PubInv/rack-mount-enclosure-for-power/display/OLED_2.4inch_51qNVxTlbsL._SL1050_.jpg

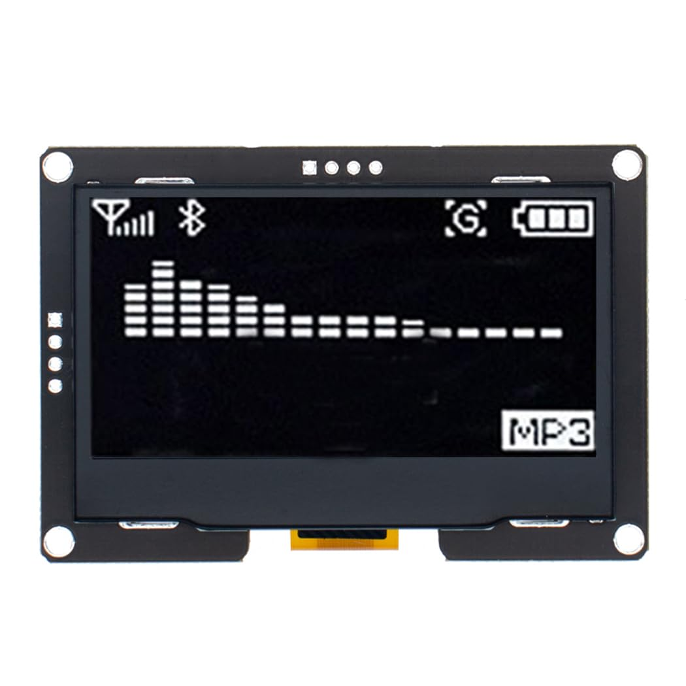
display/OLED_2.4inch_51qNVxTlbsL._SL1050_.jpg
