PubInv/rack-mount-enclosure-for-power/display/RotaryEncoder_51UYRIANXkL._SL1001_.jpg

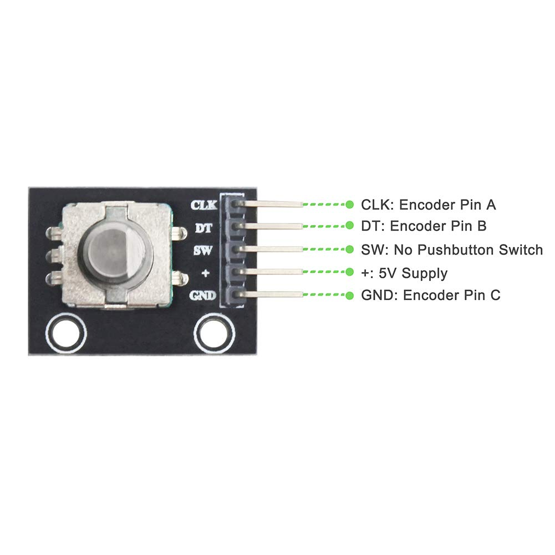
display/RotaryEncoder_51UYRIANXkL._SL1001_.jpg
