PubInv/rack-mount-enclosure-for-power/enclosure/M12BulkHead/MarkedUpDrawing.png

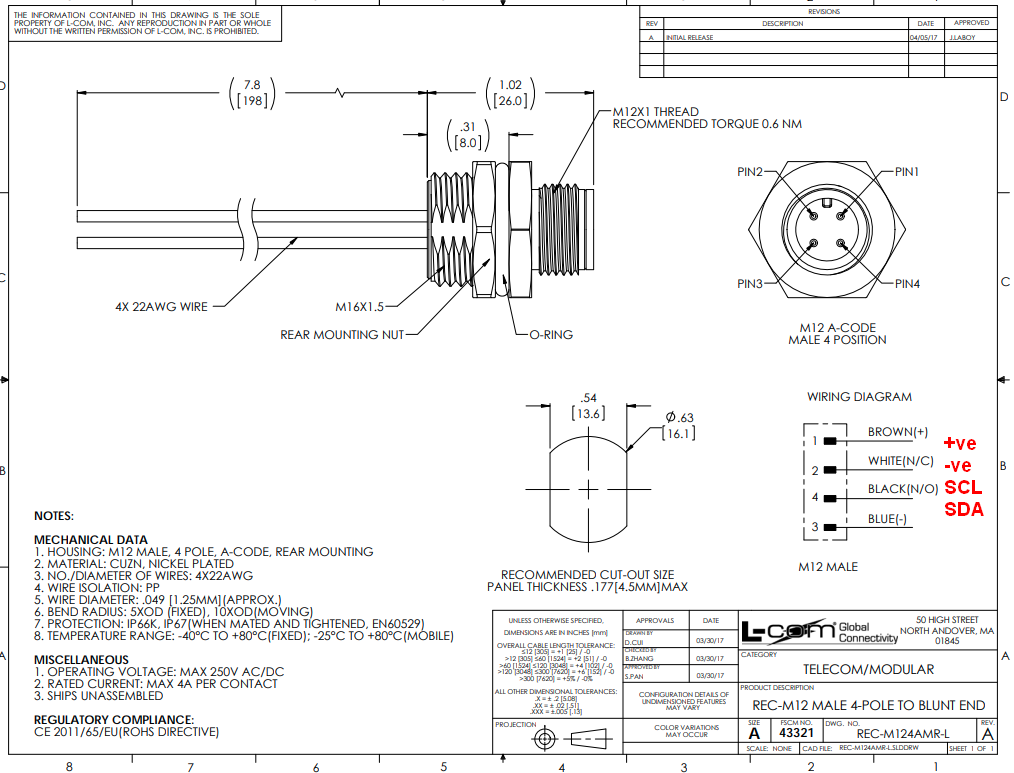
enclosure/M12BulkHead/MarkedUpDrawing.png
