PubInv/rack-mount-enclosure-for-power/enclosure/resources/41Cd8K70ImL.jpg

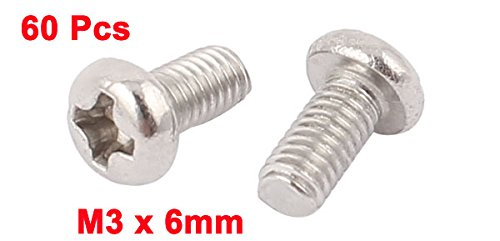
enclosure/resources/41Cd8K70ImL.jpg
