PubInv/rack-mount-enclosure-for-power/enclosure/resources/61TtXo3cijL._AC_SX679_.jpg

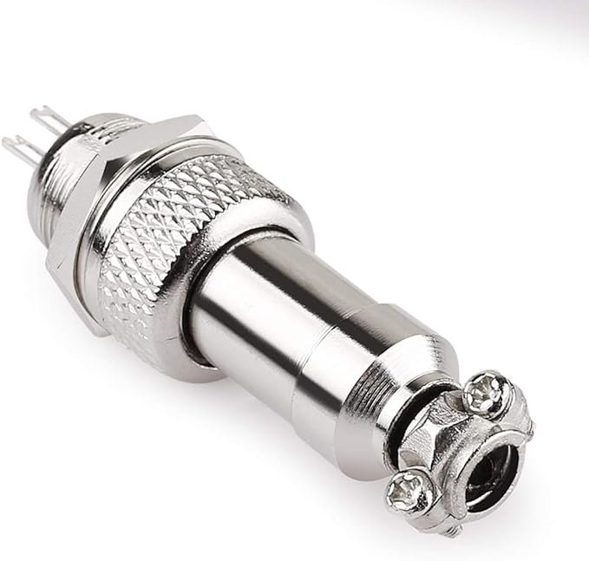
enclosure/resources/61TtXo3cijL._AC_SX679_.jpg
