PubInv/rack-mount-enclosure-for-power/enclosure/resources/PHDR-24VS.jpg

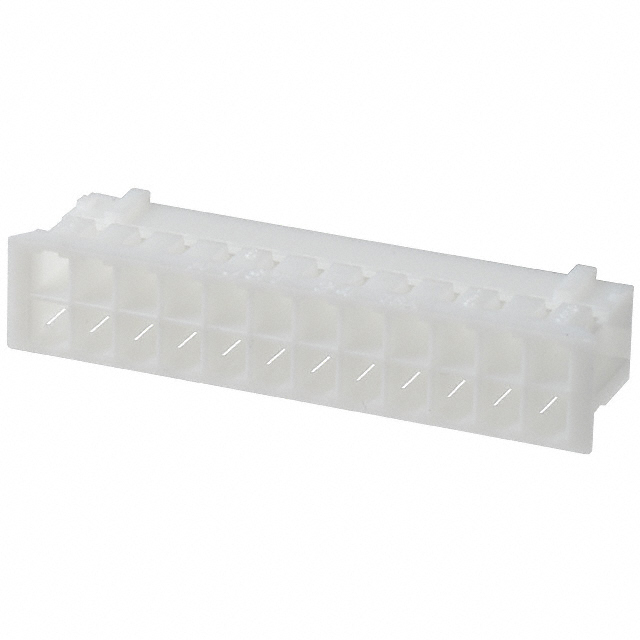
enclosure/resources/PHDR-24VS.jpg
