PubInv/rack-mount-enclosure-for-power/enclosure/Serial_Number1/SN1_Control1v1 (2).jpg

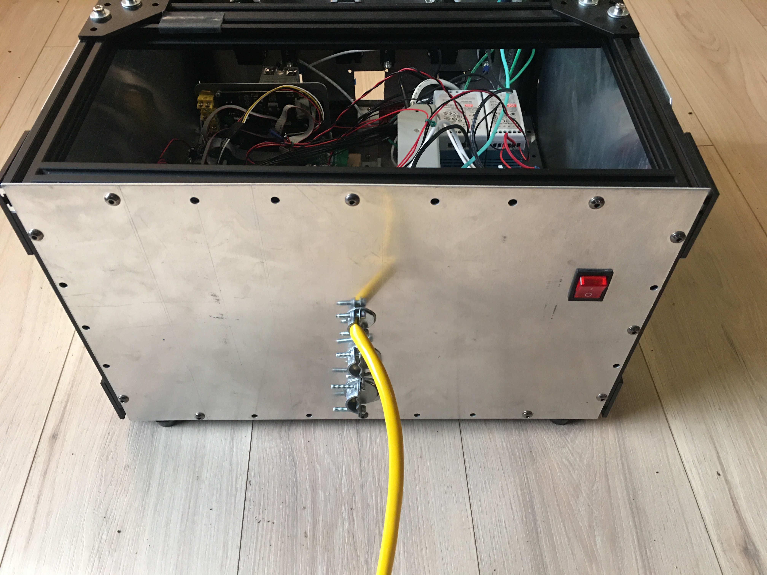
enclosure/Serial_Number1/SN1_Control1v1 (2).jpg
