PubInv/rack-mount-enclosure-for-power/enclosure/Serial_number2/Boards20230828/ThreePCB_TwoAssy.jpg

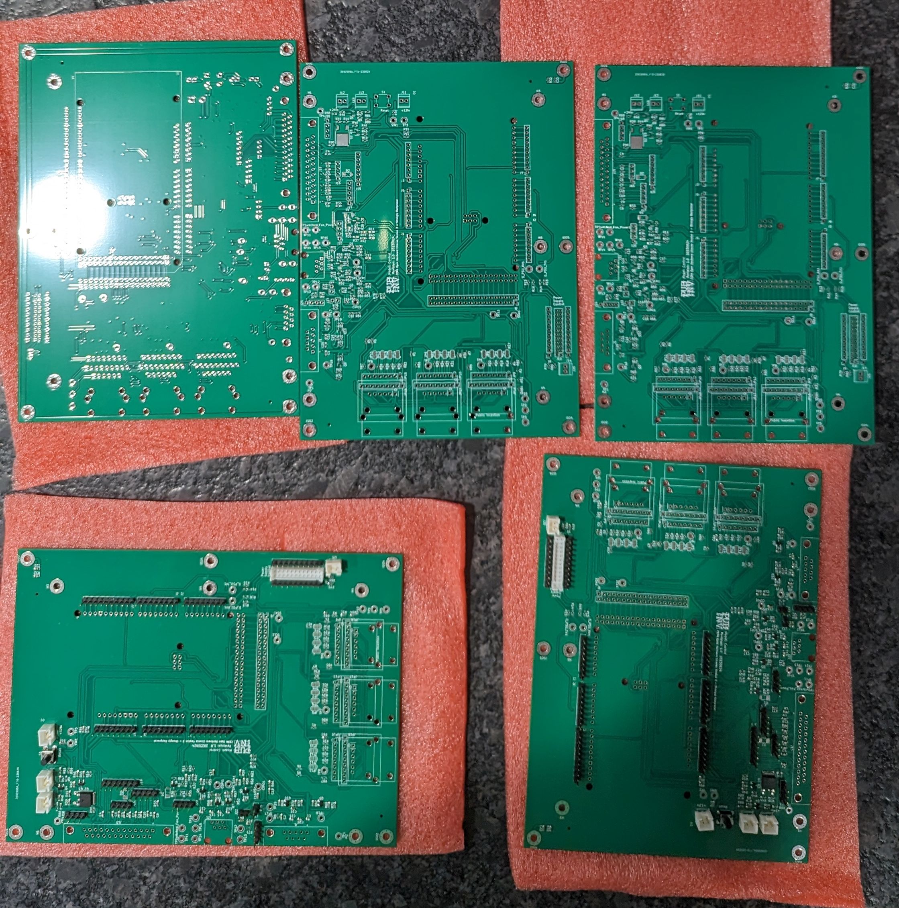
enclosure/Serial_number2/Boards20230828/ThreePCB_TwoAssy.jpg
