PubInv/rack-mount-enclosure-for-power/enclosure/Serial_number2/PXL_20230914_145754030.jpg

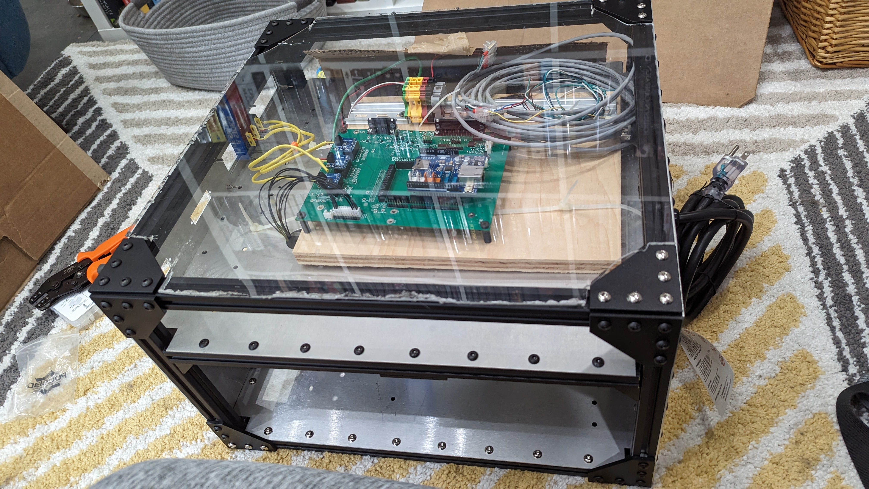
enclosure/Serial_number2/PXL_20230914_145754030.jpg
