PubInv/rack-mount-enclosure-for-power/enclosure/Serial_number2/SN2_withLoadLight.jpg

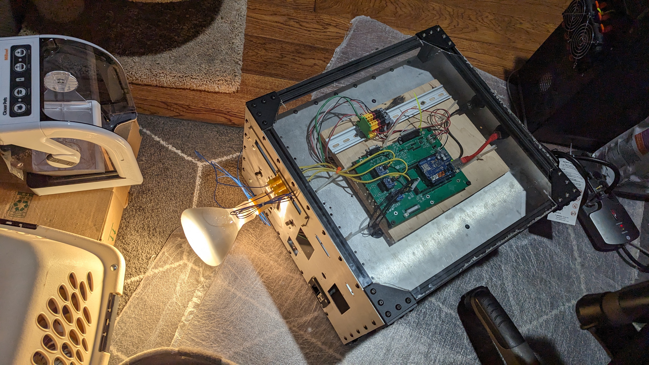
enclosure/Serial_number2/SN2_withLoadLight.jpg
