PubInv/rack-mount-enclosure-for-power/frontpanel/Parts/Anderson/PowererxPanelPlate.png

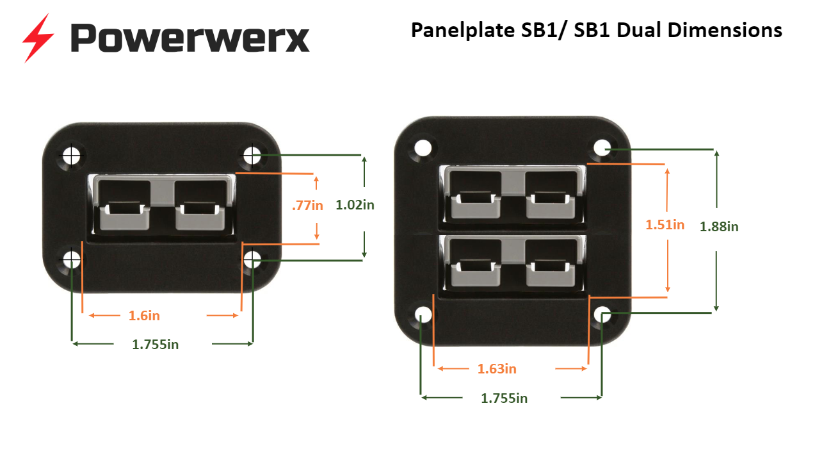
frontpanel/Parts/Anderson/PowererxPanelPlate.png
