PubInv/rack-mount-enclosure-for-power/frontpanel/Parts/Anderson_SB50_PanelDuplex.png

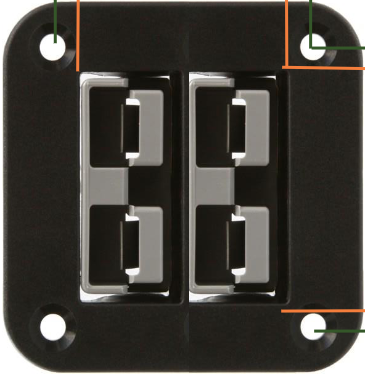
frontpanel/Parts/Anderson_SB50_PanelDuplex.png
