PubInv/rack-mount-enclosure-for-power/frontpanel/Parts/DB9Female.png

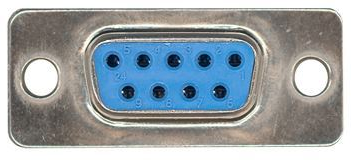
frontpanel/Parts/DB9Female.png
