PubInv/rack-mount-enclosure-for-power/frontpanel/Parts/DB25Female.png

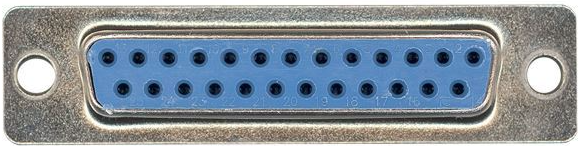
frontpanel/Parts/DB25Female.png
