PubInv/rack-mount-enclosure-for-power/frontpanel/Parts/DecoratorRecepticalCover.png

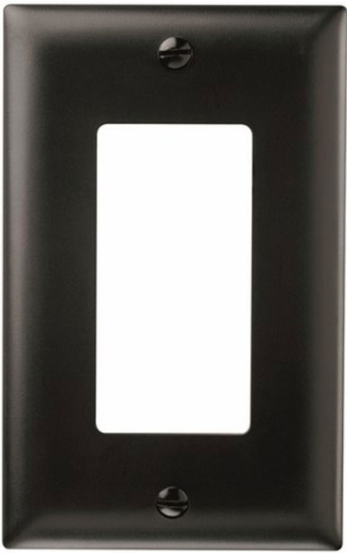
frontpanel/Parts/DecoratorRecepticalCover.png
