PubInv/rack-mount-enclosure-for-power/frontpanel/Parts/GFIReceptical.png

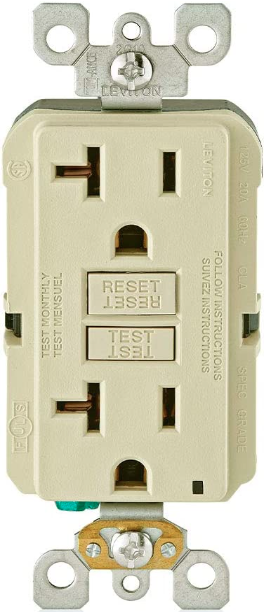
frontpanel/Parts/GFIReceptical.png
