PubInv/rack-mount-enclosure-for-power/frontpanel/Parts/Mech/DSUB9.JPG

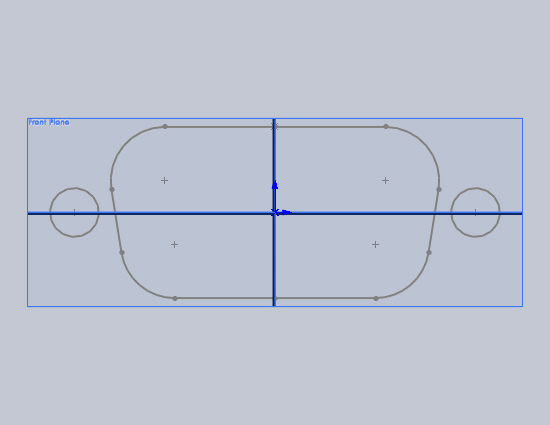
frontpanel/Parts/Mech/DSUB9.JPG
