PubInv/rack-mount-enclosure-for-power/frontpanel/Parts/Mech/GX12-Connector-Structure-01.jpg

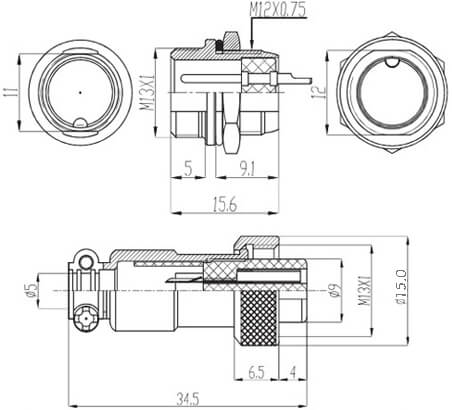
frontpanel/Parts/Mech/GX12-Connector-Structure-01.jpg
