PubInv/rack-mount-enclosure-for-power/frontpanel/Parts/Mech/IEC_Receptical/IES_Cord_220_20A.jpg

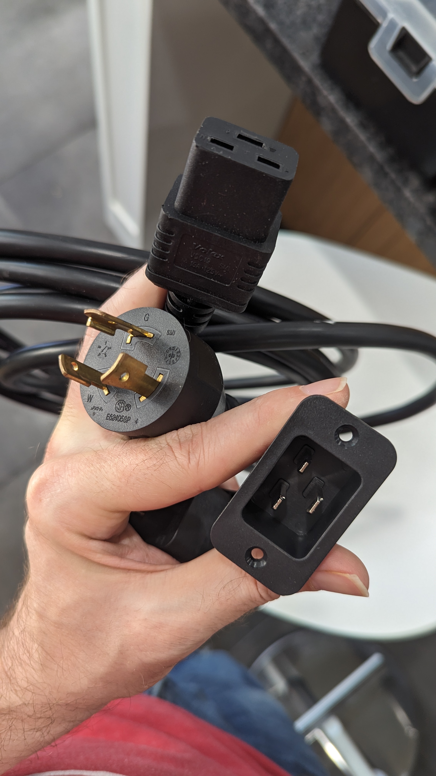
frontpanel/Parts/Mech/IEC_Receptical/IES_Cord_220_20A.jpg
