PubInv/rack-mount-enclosure-for-power/frontpanel/Parts/Mech/mpj-j-f-thermocouple/example_MJP-12-K.jpg

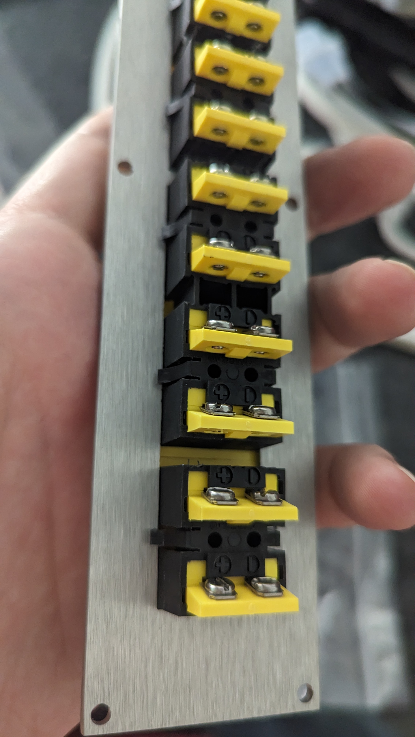
frontpanel/Parts/Mech/mpj-j-f-thermocouple/example_MJP-12-K.jpg
