PubInv/rack-mount-enclosure-for-power/frontpanel/Parts/Mech/mpj-j-f-thermocouple/example_MPJ-K-F.jpg

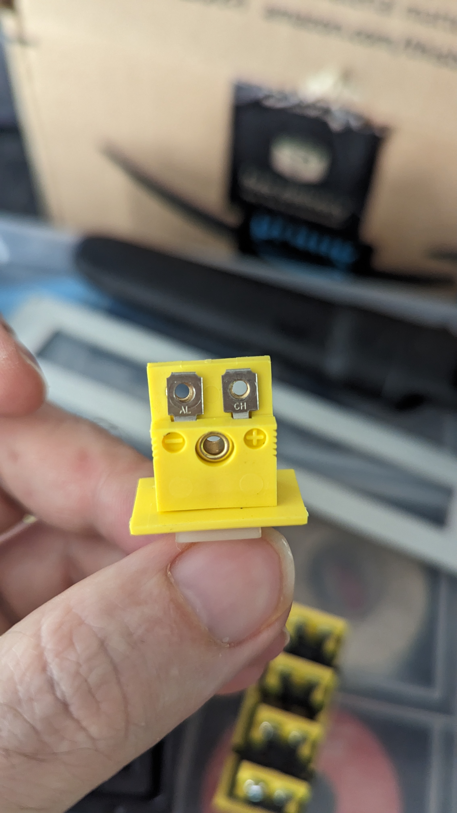
frontpanel/Parts/Mech/mpj-j-f-thermocouple/example_MPJ-K-F.jpg
