PubInv/rack-mount-enclosure-for-power/frontpanel/Parts/Mech/mpj-j-f-thermocouple/MJP-12_SketchHand.jpg

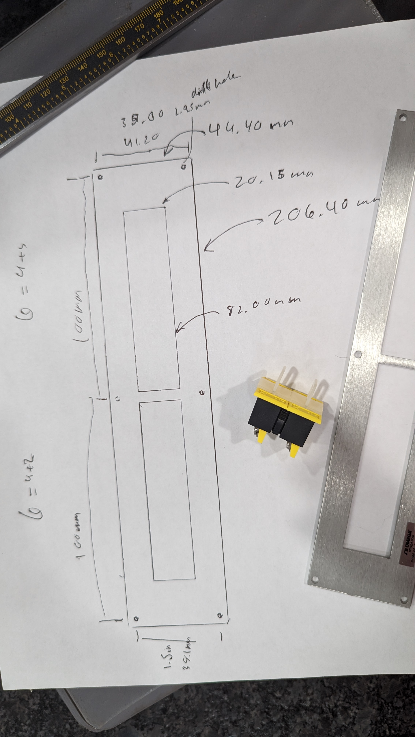
frontpanel/Parts/Mech/mpj-j-f-thermocouple/MJP-12_SketchHand.jpg
