PubInv/rack-mount-enclosure-for-power/frontpanel/Parts/Outlet/GFCI - Leviton Outlet.JPG

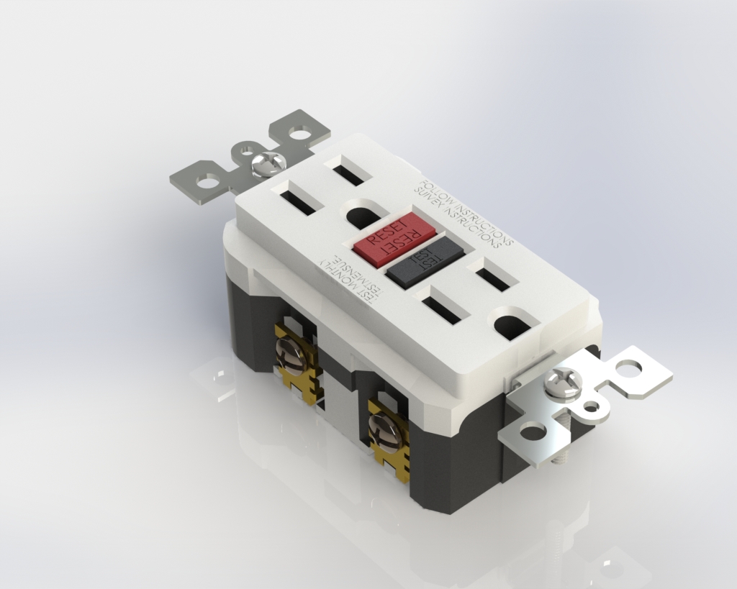
frontpanel/Parts/Outlet/GFCI - Leviton Outlet.JPG
