PubInv/rack-mount-enclosure-for-power/frontpanel/Parts/PowerSupplyDrawing.png

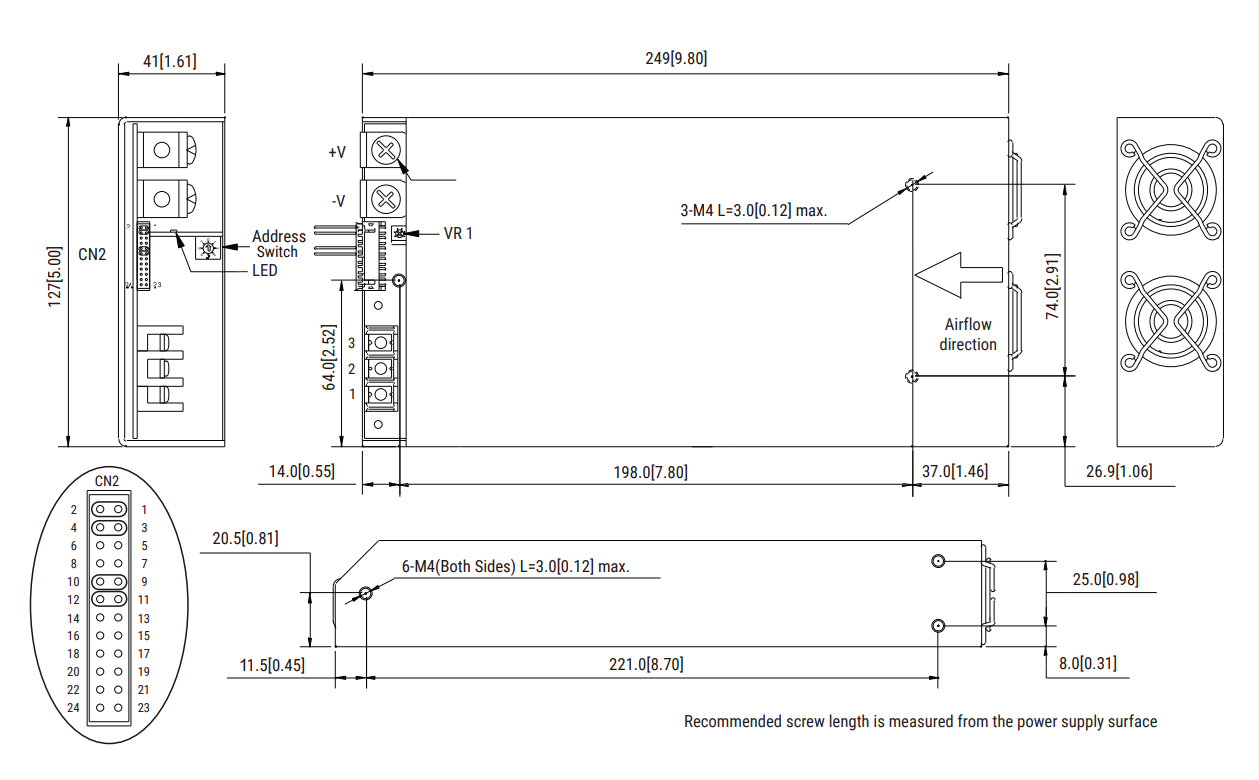
frontpanel/Parts/PowerSupplyDrawing.png
