PubInv/rack-mount-enclosure-for-power/frontpanel/Parts/RoundRockerSwitch_61Fis1CKqFL._SL1500_.jpg

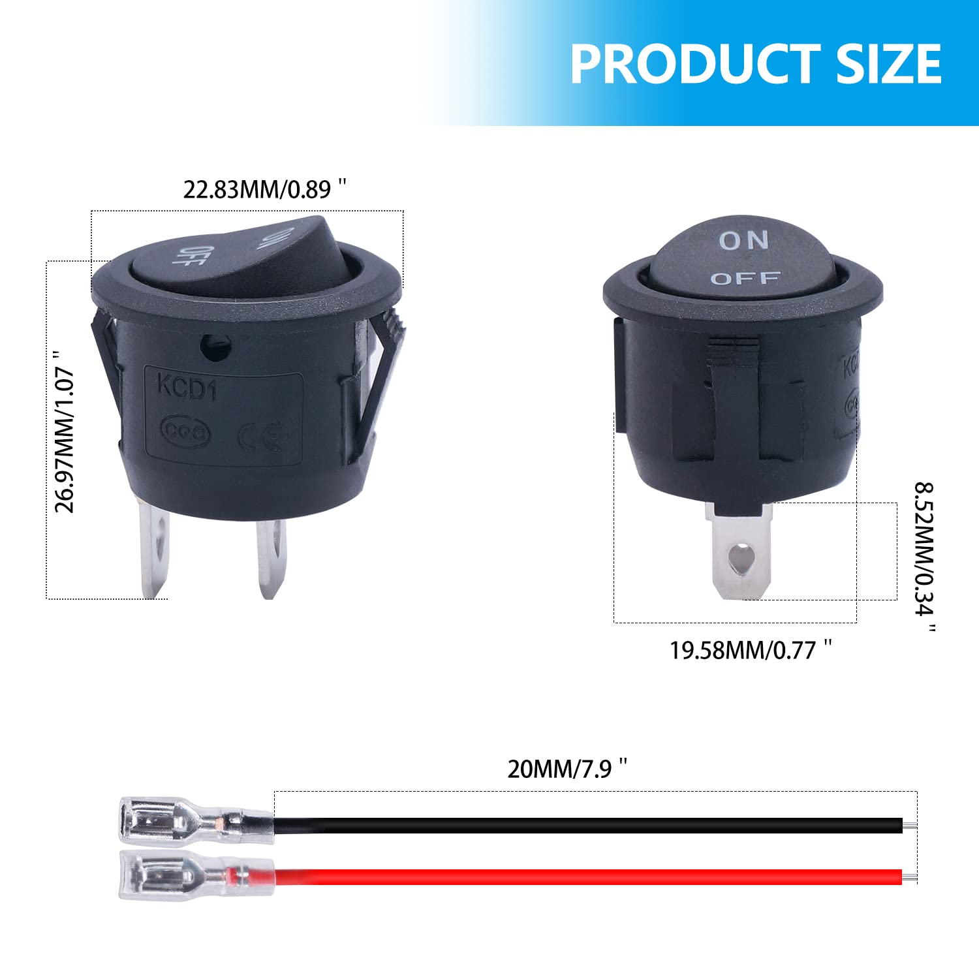
frontpanel/Parts/RoundRockerSwitch_61Fis1CKqFL._SL1500_.jpg
