PubInv/rack-mount-enclosure-for-power/frontpanel/Parts/USB_PanelMnt_51JESxIpONL._AC_SL1200_.jpg

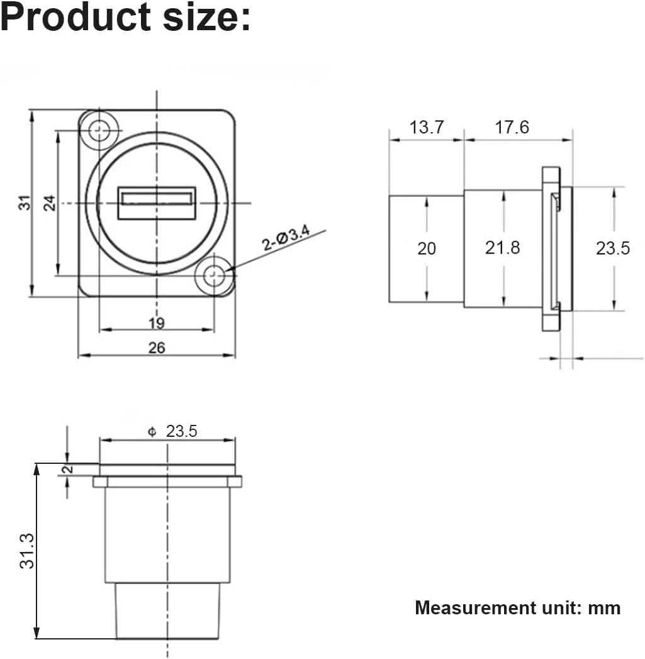
frontpanel/Parts/USB_PanelMnt_51JESxIpONL._AC_SL1200_.jpg
