PubInv/rack-mount-enclosure-for-power/frontpanel/Parts/Mech/Banana Socket (Green).step

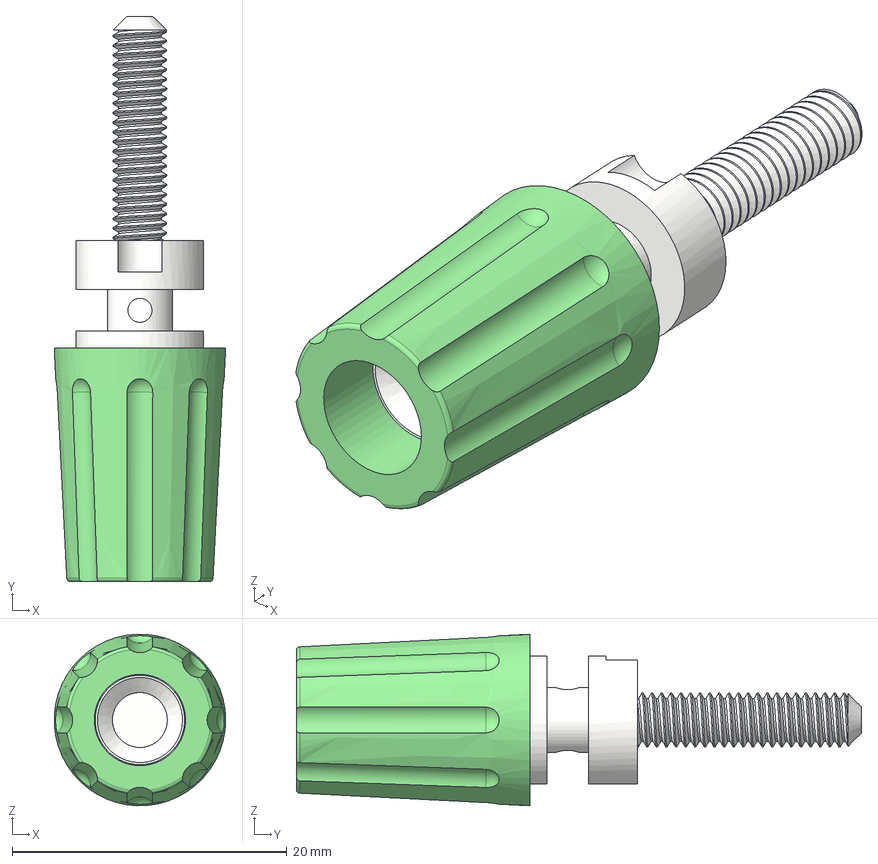
[picture p64: CAD file, 2024-09-26]
frontpanel/Parts/Mech/Banana Socket (Green).step
12.5 x 41.2 x 12.5 mm
