PubInv/rack-mount-enclosure-for-power/frontpanel/Parts/Mech/DB25_DB9/DB25_STEP/c-5747846-4-a-3d.stp

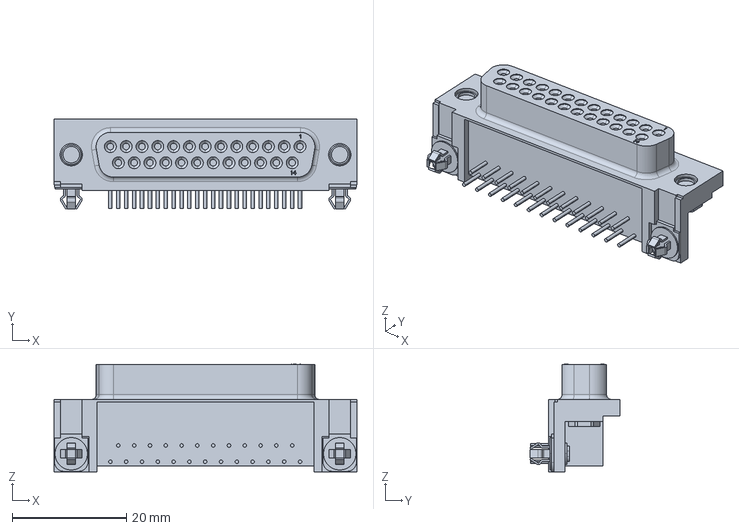
[picture p65: CAD file, 2023-08-16]
frontpanel/Parts/Mech/DB25_DB9/DB25_STEP/c-5747846-4-a-3d.stp
53.1 x 15.8 x 18.9 mm
