PubInv/rack-mount-enclosure-for-power/frontpanel/Parts/Mech/DB25_DB9/DB9_STEP/c-2311765-1-b-3d.stp

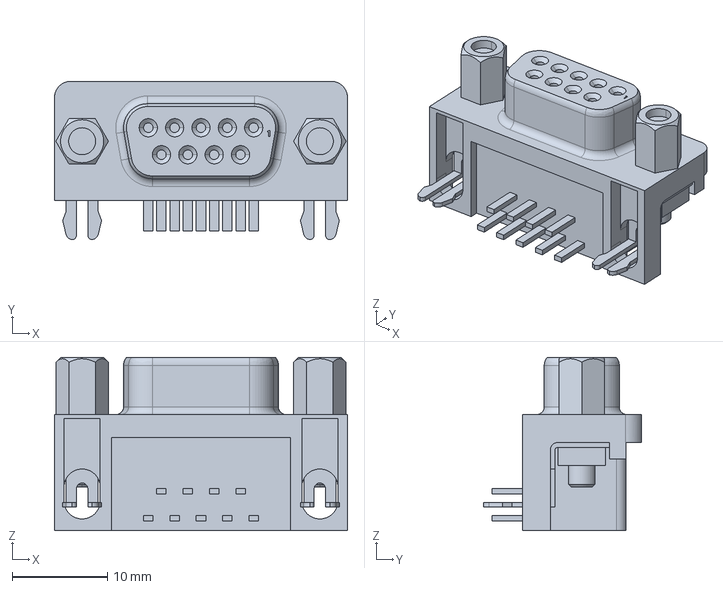
[picture p66: CAD file, 2023-08-16]
frontpanel/Parts/Mech/DB25_DB9/DB9_STEP/c-2311765-1-b-3d.stp
30.8 x 16.6 x 18.2 mm
