PubInv/rack-mount-enclosure-for-power/frontpanel/Parts/Mech/GX/gx-16-connector-4-pins-1.snapshot.3/GX-16 Connector 4 Pins.stp

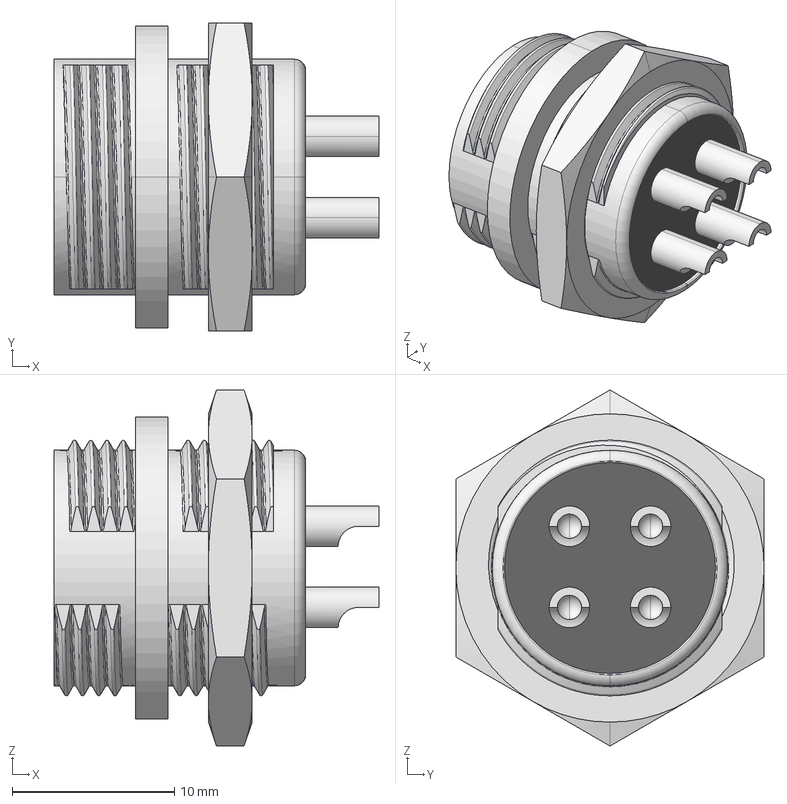
[picture p67: CAD file, 2024-09-26]
frontpanel/Parts/Mech/GX/gx-16-connector-4-pins-1.snapshot.3/GX-16 Connector 4 Pins.stp
20.0 x 19.0 x 21.9 mm
Nut
Isolator
Pins
