PubInv/rack-mount-enclosure-for-power/frontpanel/Parts/Mech/GX/gx12-4-1.snapshot.1/GX12.stp

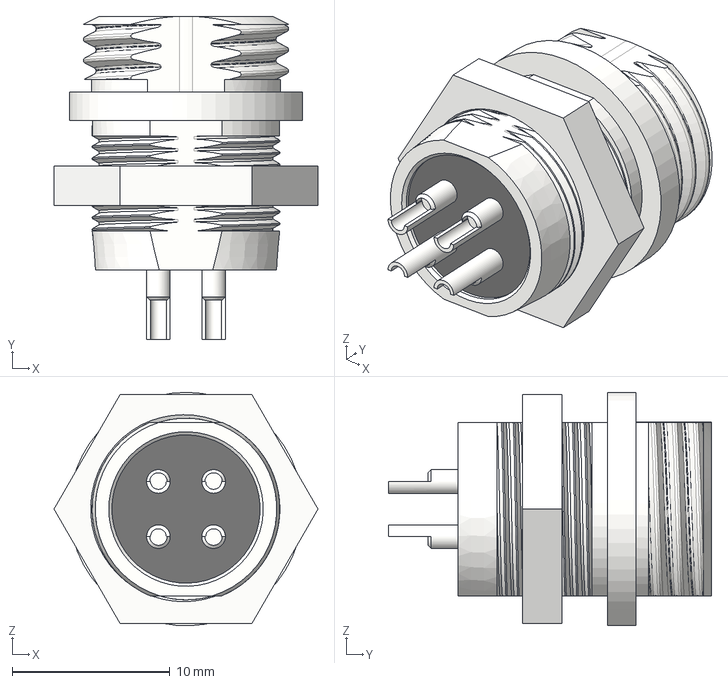
[picture p68: CAD file, 2024-09-26]
frontpanel/Parts/Mech/GX/gx12-4-1.snapshot.1/GX12.stp
16.7 x 20.5 x 14.8 mm
