PubInv/rack-mount-enclosure-for-power/frontpanel/Parts/Mech/IEC_Receptical/C14/e_0870.0001i002.step

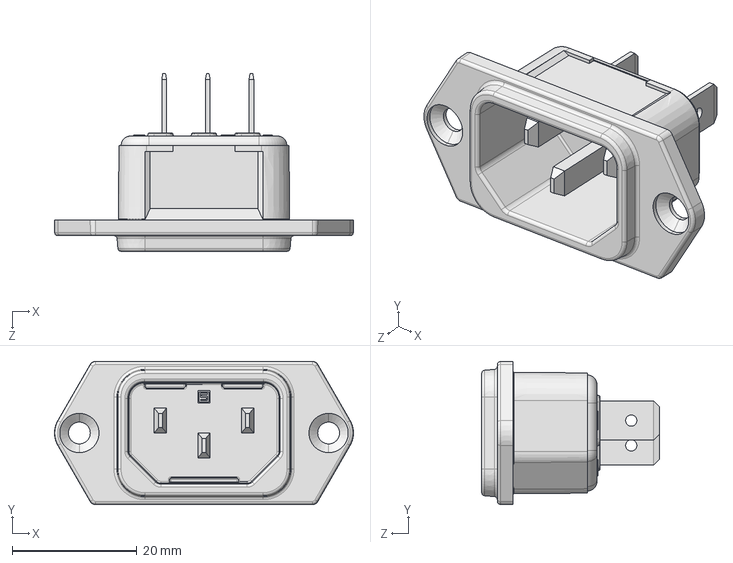
[picture p69: CAD file, 2023-08-16]
frontpanel/Parts/Mech/IEC_Receptical/C14/e_0870.0001i002.step
48.0 x 23.0 x 28.5 mm
