PubInv/rack-mount-enclosure-for-power/frontpanel/Parts/Mech/IEC_Receptical/C20/e_0100.6436a002.step

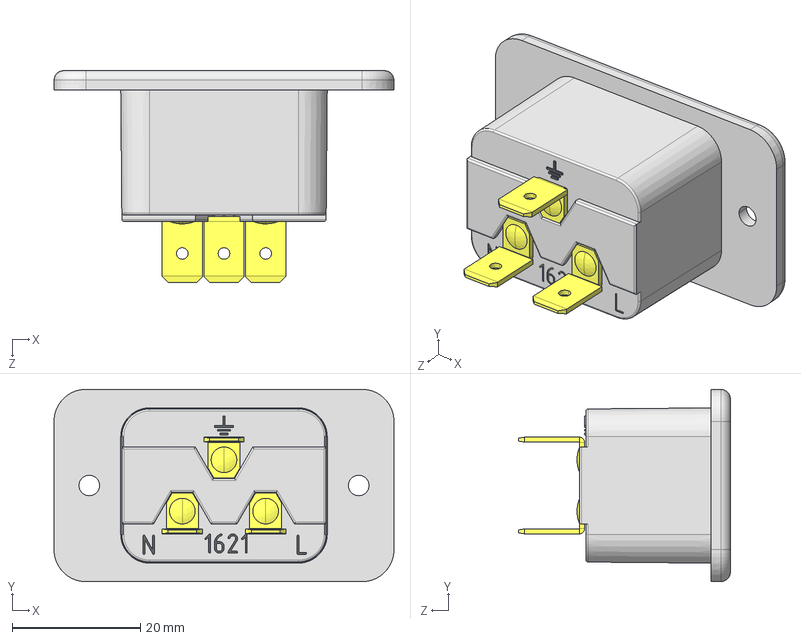
[picture p70: CAD file, 2023-08-16]
frontpanel/Parts/Mech/IEC_Receptical/C20/e_0100.6436a002.step
53.0 x 30.0 x 33.0 mm
