PubInv/rack-mount-enclosure-for-power/frontpanel/Parts/Mech/LIB_PM5R3-BC/PM5R3-BC/3D/PM5R3-BC.stp

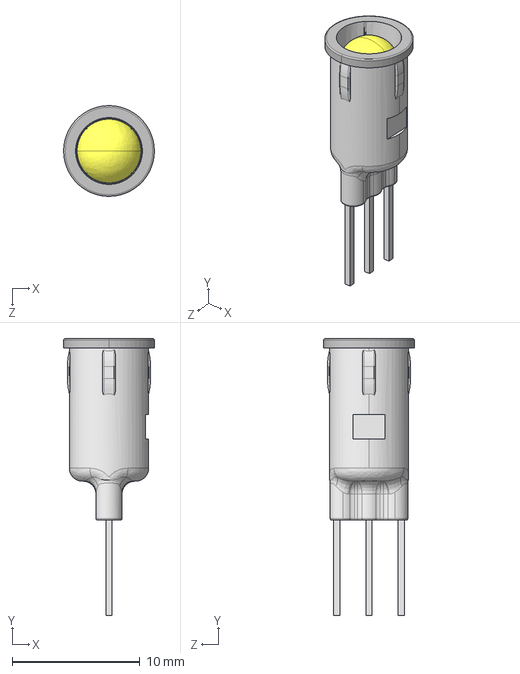
[picture p71: CAD file, 2023-08-03]
frontpanel/Parts/Mech/LIB_PM5R3-BC/PM5R3-BC/3D/PM5R3-BC.stp
7.11 x 21.7 x 7.11 mm
3 lead LED
PM5-3_A1
