PubInv/rack-mount-enclosure-for-power/frontpanel/Parts/Mech/mpj-j-f-thermocouple/JackPanel_MJP.FCStd

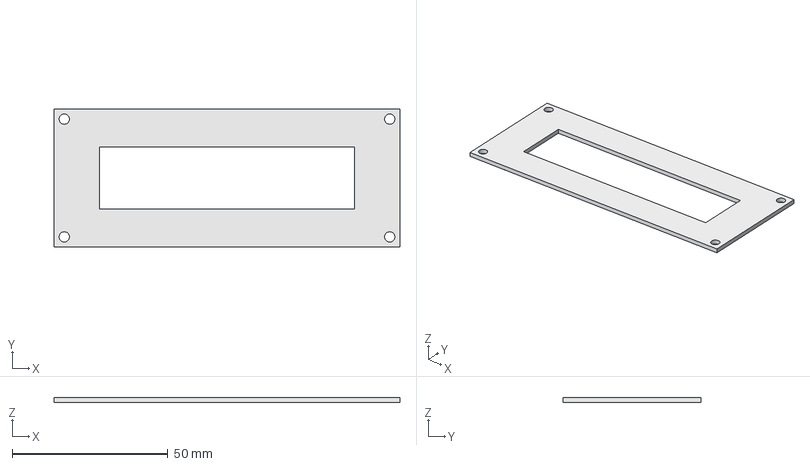
[picture p72: CAD file, 2023-08-17]
frontpanel/Parts/Mech/mpj-j-f-thermocouple/JackPanel_MJP.FCStd
111.3 x 44.4 x 1.59 mm
