PubInv/rack-mount-enclosure-for-power/frontpanel/Parts/PowerWerx/PanelPlate_SB-PartBodySB1.step

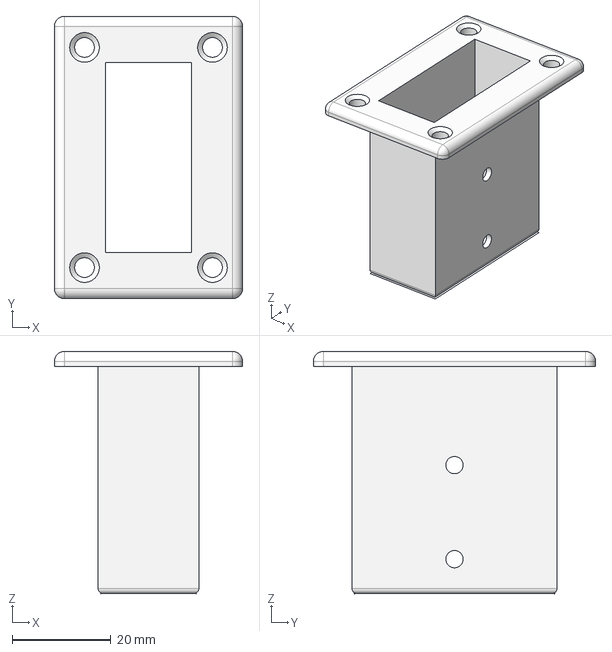
[picture p73: CAD file, 2023-08-16]
frontpanel/Parts/PowerWerx/PanelPlate_SB-PartBodySB1.step
38.1 x 57.1 x 49.0 mm
