PubInv/rack-mount-enclosure-for-power/Plant20x30inch/O2Quick.FCStd

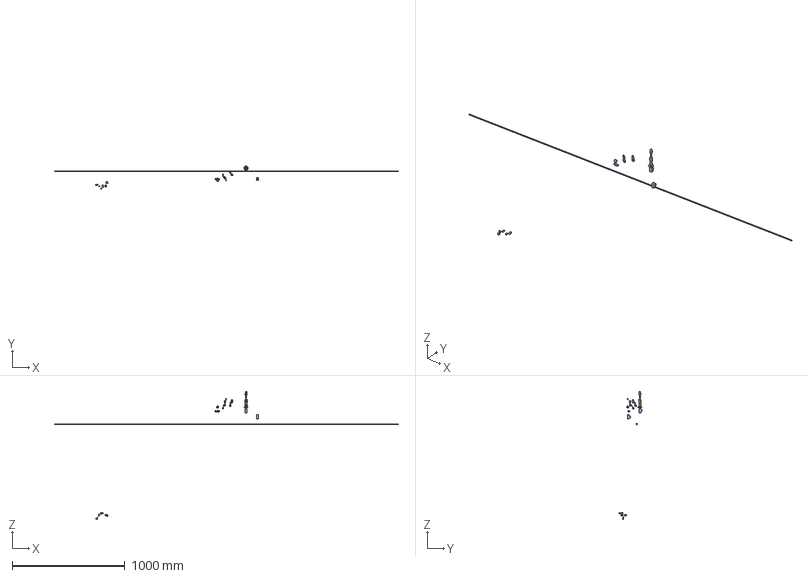
[picture p74: CAD file, 2024-12-17]
Plant20x30inch/O2Quick.FCStd
3048.0 x 206.5 x 1138.0 mm
7934A6_Quick-Disconnect Hose Coupling Set for Compre1_7934A6_Quick-Disconnect Hose Coupling Set for Compre_001
7934A6_Quick-Disconnect Hose Coupling Set for Compre1_7934A6_Quick-Disconnect Hose Coupling Set for Compre003_001
9151K42_High-Pressure Nickel-Plated Brass Pipe Fitting1_9151K42_High-Pressure Nickel-Plated Brass Pipe Fitting_001
95611A286_Chemical-Resistant PVC Plastic Washer1_95611A286_Chemical-Resistant PVC Plastic Washer_001
5272K191_Yor-Lok Fitting for Copper Tubing1_5272K191_Yor-Lok Fitting for Copper Tubing_001
5272K191_Yor-Lok Fitting for Copper Tubing1_5272K191_Yor-Lok Fitting for Copper Tubing001_001
5272K191_Yor-Lok Fitting for Copper Tubing1_5272K191_Yor-Lok Fitting for Copper Tubing002_001
5272K191_Yor-Lok Fitting for Copper Tubing1_5272K191_Yor-Lok Fitting for Copper Tubing003_001
5305K401_Yor-Lok Fitting for Stainless Steel Tubing1_5305K401_Yor-Lok Fitting for Stainless Steel Tubing_001
5305K401_Yor-Lok Fitting for Stainless Steel Tubing1_5305K401_Yor-Lok Fitting for Stainless Steel Tubing001_001
5305K401_Yor-Lok Fitting for Stainless Steel Tubing1_5305K401_Yor-Lok Fitting for Stainless Steel Tubing002_001
5305K401_Yor-Lok Fitting for Stainless Steel Tubing1_5305K401_Yor-Lok Fitting for Stainless Steel Tubing003_001
5305K401_Yor-Lok Fitting for Stainless Steel Tubing1_5305K401_Yor-Lok Fitting for Stainless Steel Tubing004_001
5305K401_Yor-Lok Fitting for Stainless Steel Tubing1_5305K401_Yor-Lok Fitting for Stainless Steel Tubing005_001
5305K401_Yor-Lok Fitting for Stainless Steel Tubing1_5305K401_Yor-Lok Fitting for Stainless Steel Tubing006_001
7919A51_Hose Fitting for Compressed Gas1_7919A51_Hose Fitting for Compressed Gas_001
7919A51_Hose Fitting for Compressed Gas1_7919A51_Hose Fitting for Compressed Gas001_001
8955K31_General Purpose Copper Tubing1_8955K31_General Purpose Copper Tubing_001
9137K71_Fast-Acting Pressure-Relief Valve1_9137K71_Fast-Acting Pressure-Relief Valve_001
9137K71_Fast-Acting Pressure-Relief Valve1_9137K71_Fast-Acting Pressure-Relief Valve001_001
9137K71_Fast-Acting Pressure-Relief Valve1_9137K71_Fast-Acting Pressure-Relief Valve002_001
9137K71_Fast-Acting Pressure-Relief Valve1_9137K71_Fast-Acting Pressure-Relief Valve003_001
9137K71_Fast-Acting Pressure-Relief Valve1_9137K71_Fast-Acting Pressure-Relief Valve004_001
9137K71_Fast-Acting Pressure-Relief Valve1_9137K71_Fast-Acting Pressure-Relief Valve005_001
9137K71_Fast-Acting Pressure-Relief Valve1_9137K71_Fast-Acting Pressure-Relief Valve006_001
9151K42_High-Pressure Nickel-Plated Brass Pipe Fitting1_9151K42_High-Pressure Nickel-Plated Brass Pipe Fitting_002
