PubInv/rack-mount-enclosure-for-power/display/rotary+encoder_17mm_hole_spc.stp

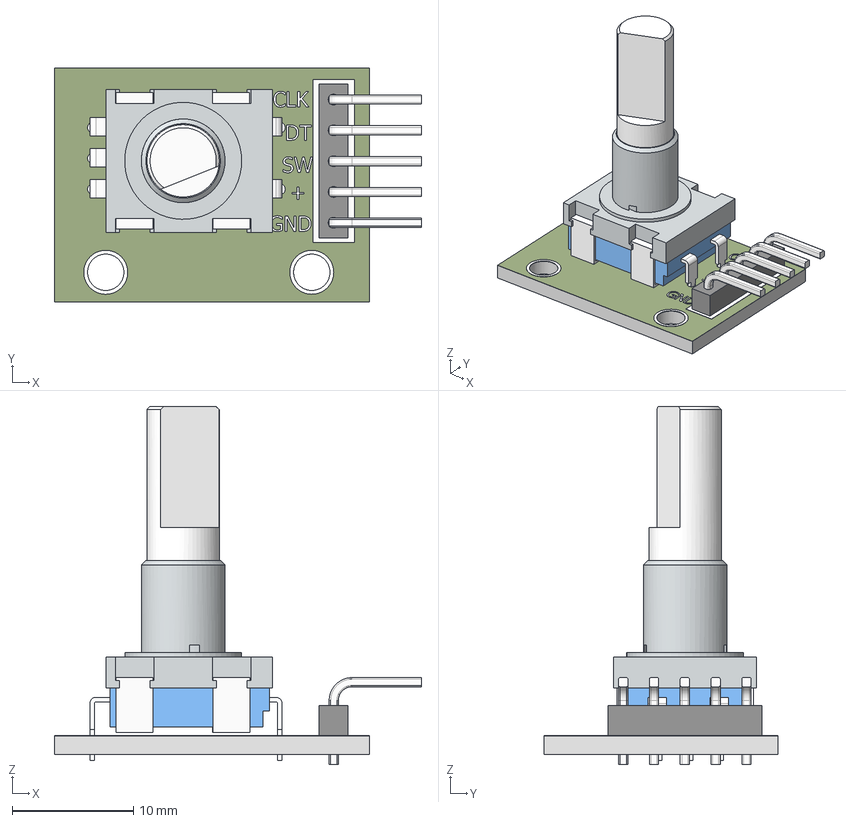
[picture p75: CAD file, 2025-04-03]
display/rotary+encoder_17mm_hole_spc.stp
30.3 x 19.3 x 29.6 mm
pcb
mtg flange
body_encoder
5 pin header
90d pin_header x 5
decal_encoder
pins_encoder body_2 x 5
shaft_encoder
