PubInv/rack-mount-enclosure-for-power/enclosure/FreeCADAssy/ControllerSupportRT/ControllerSupportRT.FCStd

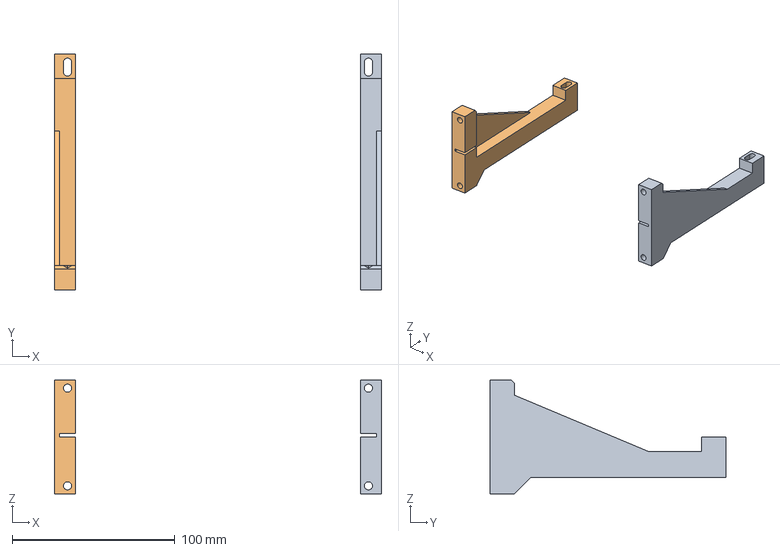
[picture p76: CAD file, 2023-09-08]
enclosure/FreeCADAssy/ControllerSupportRT/ControllerSupportRT.FCStd
201.0 x 145.0 x 70.0 mm
BodySupportRT
CloneBodySupportLR
