PubInv/rack-mount-enclosure-for-power/enclosure/FreeCADAssy/Extrusions_Simple.FCStd

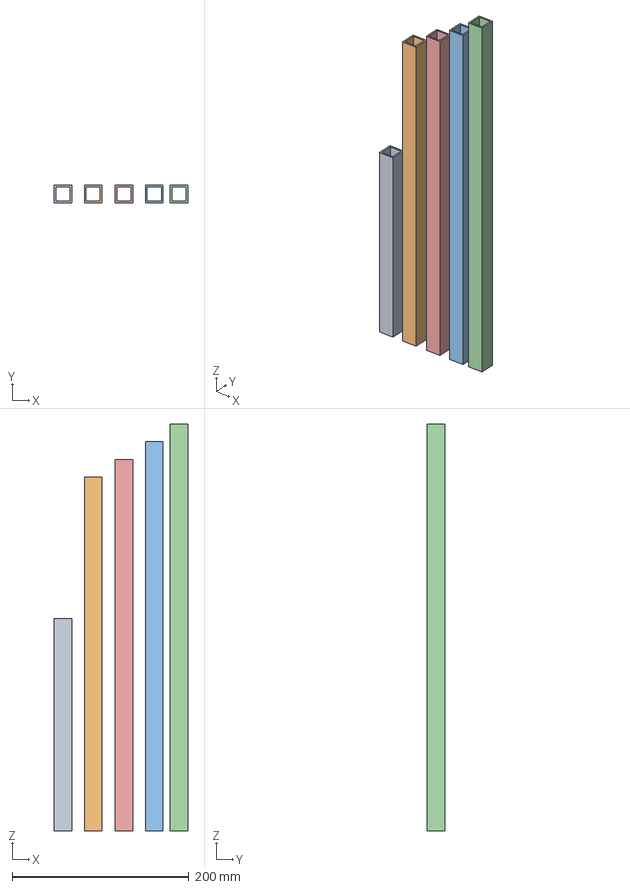
[picture p77: CAD file, 2023-08-03]
enclosure/FreeCADAssy/Extrusions_Simple.FCStd
151.0 x 20.0 x 460.0 mm
Body20x20x240Tube
Body20x20x400Tube
Body20x20x440
Body20x20x460
Body20x20x420Tube
