PubInv/rack-mount-enclosure-for-power/enclosure/MeanWell/ALIM MEAN WELL MDR-10-12.STEP

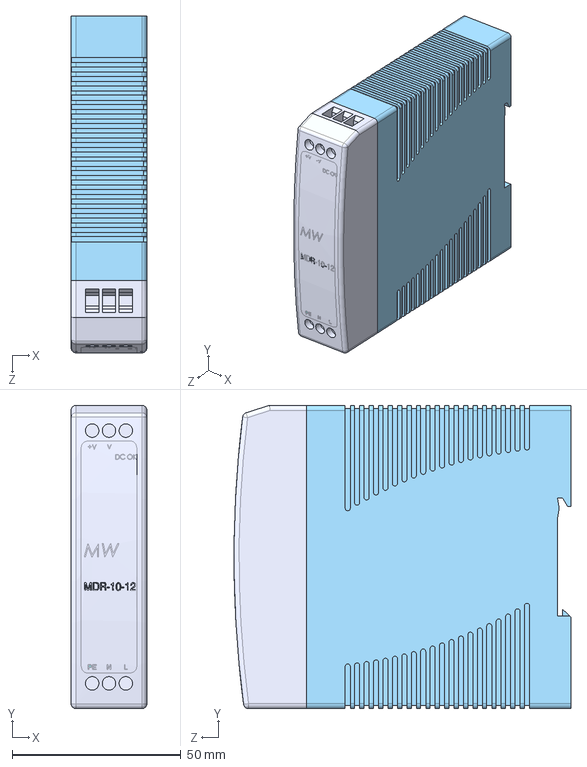
[picture p78: CAD file, 2023-10-19]
enclosure/MeanWell/ALIM MEAN WELL MDR-10-12.STEP
22.5 x 90.0 x 100.0 mm
