PubInv/rack-mount-enclosure-for-power/enclosure/SSR_2D3D_538 B/2D3D 538 B.stp

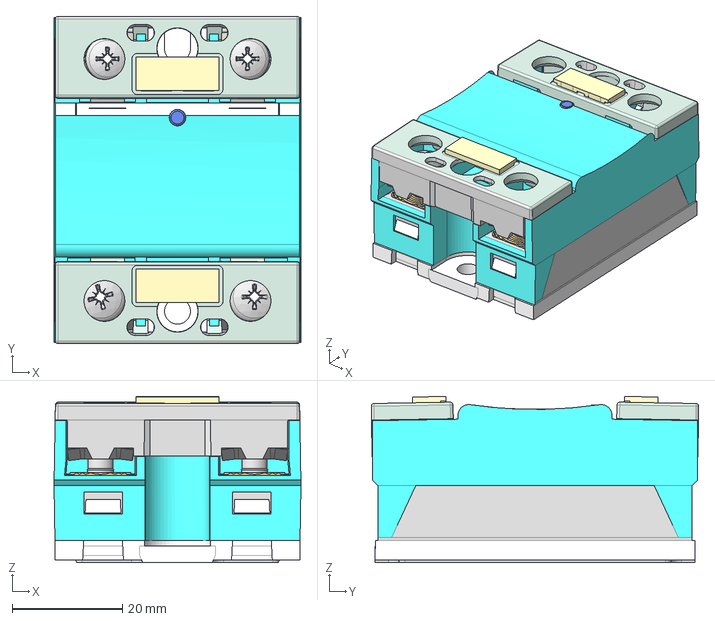
[picture p79: CAD file, 2023-10-19]
enclosure/SSR_2D3D_538 B/2D3D 538 B.stp
44.8 x 59.4 x 30.1 mm
