PubInv/rack-mount-enclosure-for-power/enclosure/ThreeU/ThreeU_Chassis-BodyFrontPanelWithHoles20241002.step

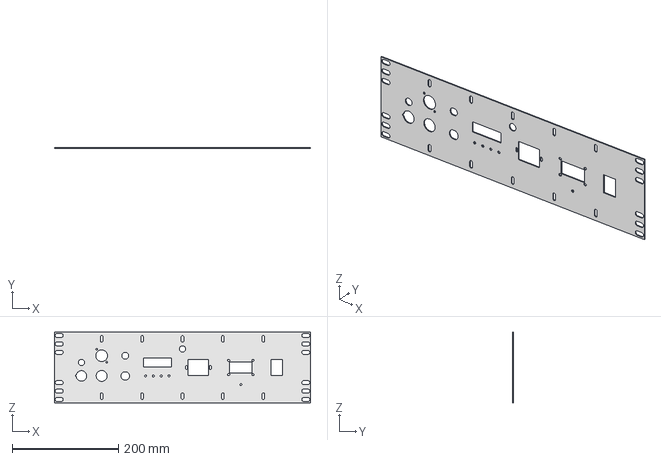
[picture p80: CAD file, 2024-10-02]
enclosure/ThreeU/ThreeU_Chassis-BodyFrontPanelWithHoles20241002.step
482.6 x 1.59 x 133.3 mm
