PubInv/rack-mount-enclosure-for-power/enclosure/TwoU/TwoU_Chassis-PartChassisBodyChassis_18x8_5.stl

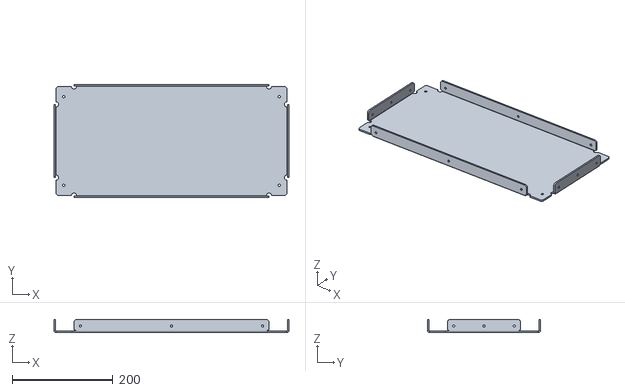
[picture p81: CAD file, 2023-10-18]
enclosure/TwoU/TwoU_Chassis-PartChassisBodyChassis_18x8_5.stl
465.5 x 224.2 x 25.5
