PubInv/rack-mount-enclosure-for-power/frontpanel/Parts/Mech/80MM_FAN.step

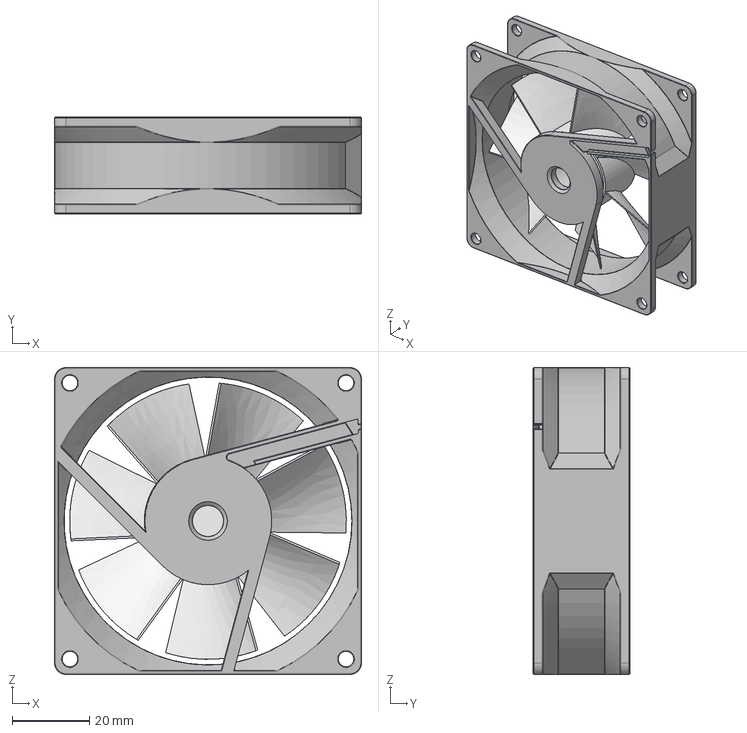
[picture p82: CAD file, 2024-07-04]
frontpanel/Parts/Mech/80MM_FAN.step
79.5 x 25.0 x 79.5 mm
