PubInv/rack-mount-enclosure-for-power/frontpanel/Parts/PowerWerx/PanelPlate_SB.FCStd

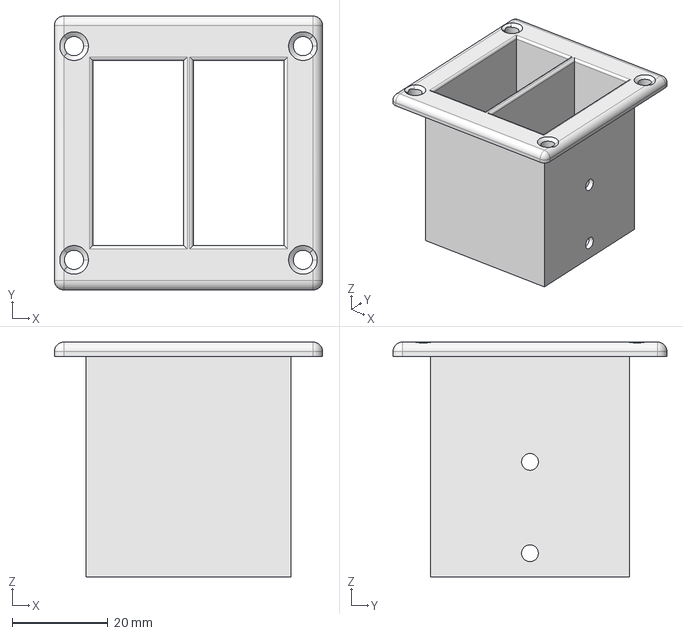
[picture p84: CAD file, 2023-08-16]
frontpanel/Parts/PowerWerx/PanelPlate_SB.FCStd
56.0 x 57.1 x 49.0 mm
