PubInv/rack-mount-enclosure-for-power/frontpanel/rear panel edit 1_3.dxf

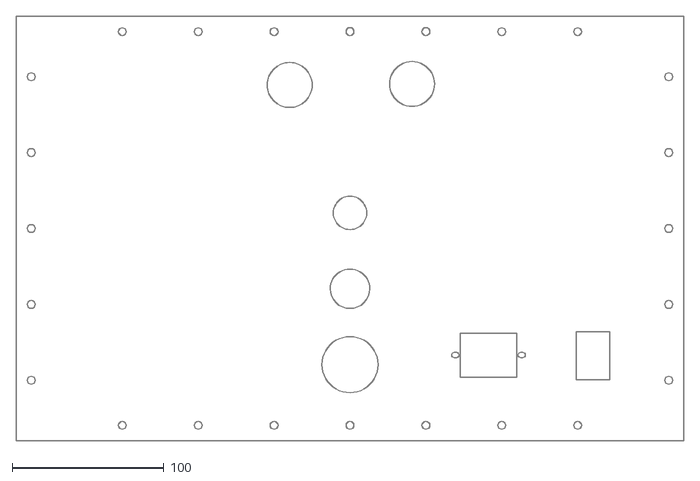
[picture p85: CAD file, 2023-08-17]
frontpanel/rear panel edit 1_3.dxf
440.0 x 279.4
