PubInv/rack-mount-enclosure-for-power/enclosure/3D models/enclosure_15.stl

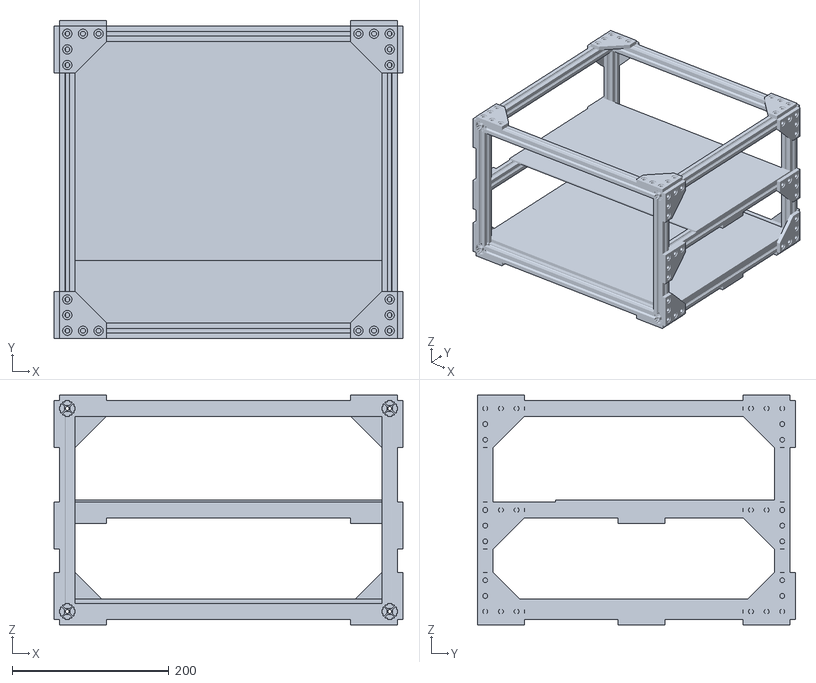
[picture p86: CAD file, 2023-04-13]
enclosure/3D models/enclosure_15.stl
445.8 x 406.4 x 293.4
