PubInv/rack-mount-enclosure-for-power/enclosure/TwoU/TwoU_Chassis-FrontPanel_2U.stl

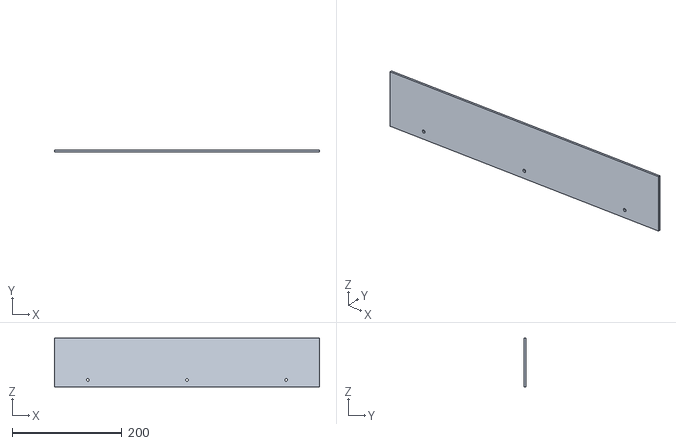
[picture p87: CAD file, 2023-10-18]
enclosure/TwoU/TwoU_Chassis-FrontPanel_2U.stl
482.6 x 3.18 x 88.9
