PubInv/rack-mount-enclosure-for-power/frontpanel/frontpanel.FCStd

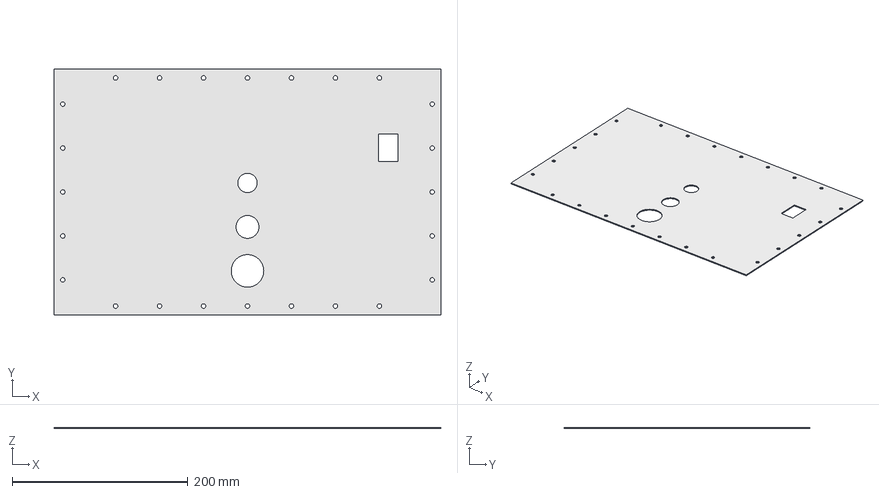
[picture p88: CAD file, 2023-08-02]
frontpanel/frontpanel.FCStd
440.0 x 279.4 x 1.57 mm
