PubInv/rack-mount-enclosure-for-power/frontpanel/Parts/Mech/Gusseted 2020 corner bracket v2.step

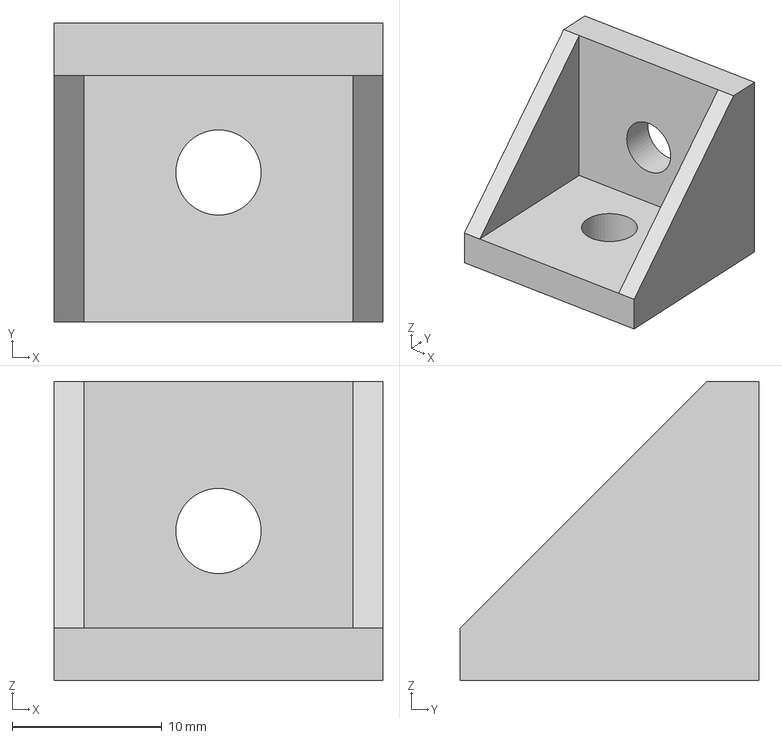
[picture p89: CAD file, 2023-08-03]
frontpanel/Parts/Mech/Gusseted 2020 corner bracket v2.step
22.0 x 20.0 x 20.0 mm
