PubInv/rack-mount-enclosure-for-power/frontpanel/Parts/Mech/mpj-j-f-thermocouple/MPJ-K-F.STEP

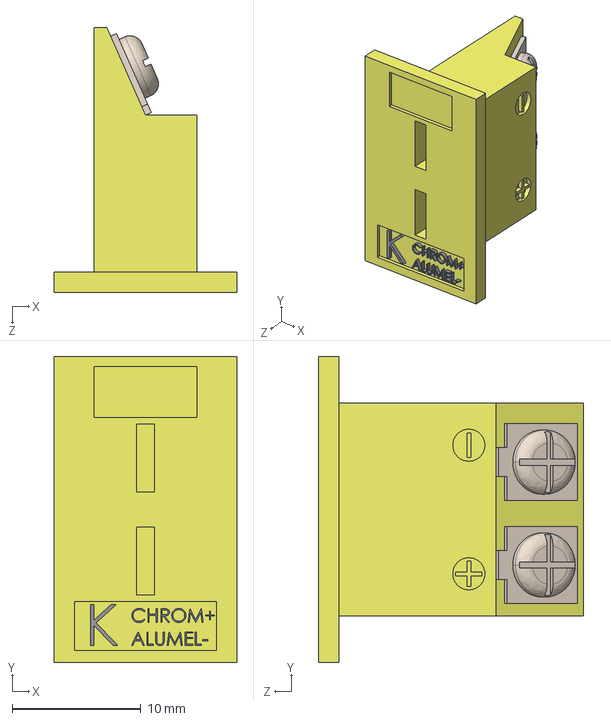
[picture p90: CAD file, 2023-04-01]
frontpanel/Parts/Mech/mpj-j-f-thermocouple/MPJ-K-F.STEP
14.2 x 23.8 x 20.6 mm
