PubInv/rack-mount-enclosure-for-power/Plant20x30inch/Entabulator10x15.FCStd

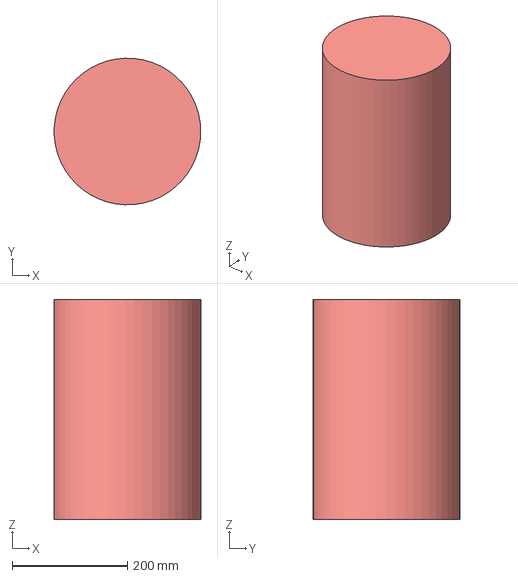
[picture p91: CAD file, 2024-07-16]
Plant20x30inch/Entabulator10x15.FCStd
253.8 x 253.9 x 381.0 mm
