PubInv/rack-mount-enclosure-for-power/enclosure/3D models/enclosure.stl

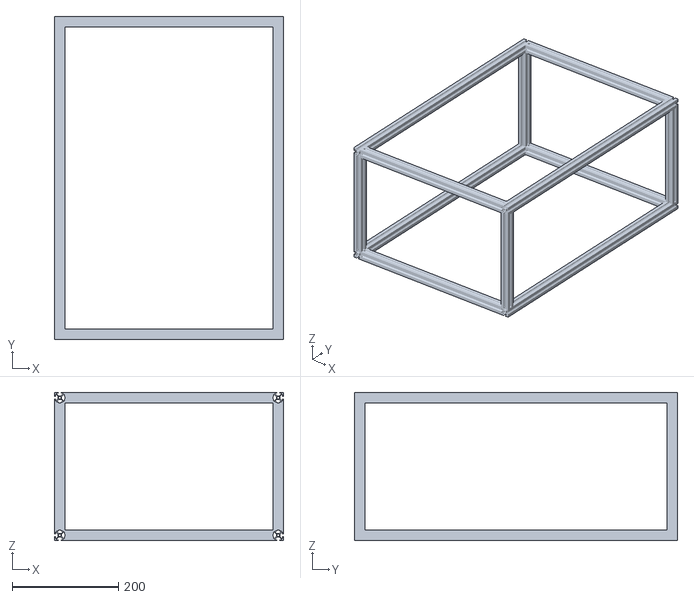
[picture p92: CAD file, 2023-03-29]
enclosure/3D models/enclosure.stl
431.8 x 609.6 x 279.4
