PubInv/rack-mount-enclosure-for-power/enclosure/ThreeU/ThreeU_Chassis-BodySidePanel20240630_1804.step

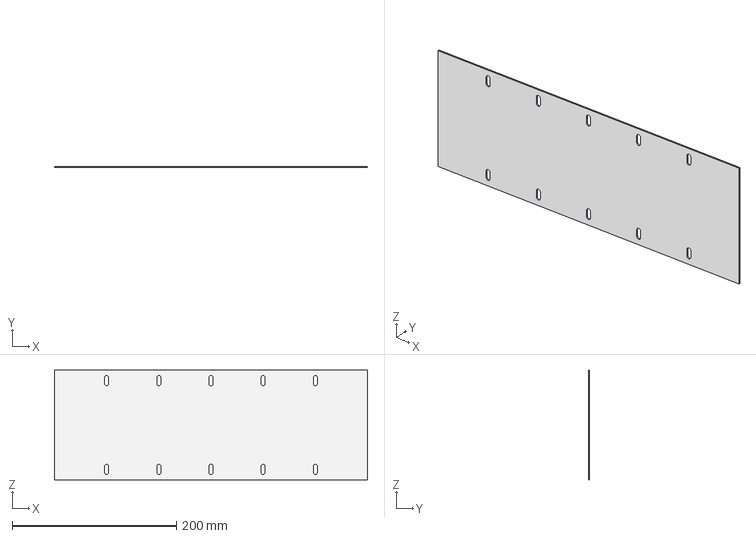
[picture p93: CAD file, 2024-07-08]
enclosure/ThreeU/ThreeU_Chassis-BodySidePanel20240630_1804.step
381.0 x 1.59 x 133.3 mm
