PubInv/rack-mount-enclosure-for-power/frontpanel/frontpanel-PartBottomPlateV2.oBodyBottomPlateV2.step

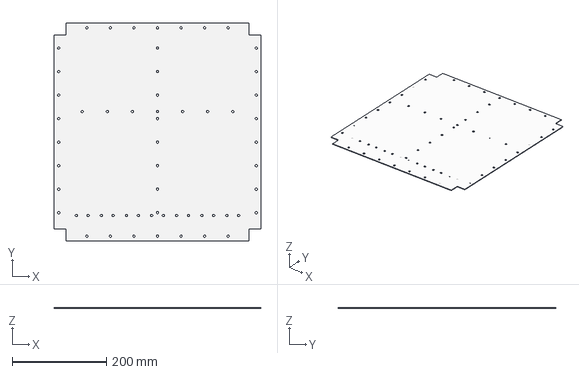
[picture p94: CAD file, 2023-08-01]
frontpanel/frontpanel-PartBottomPlateV2.oBodyBottomPlateV2.step
440.0 x 463.0 x 1.57 mm
