PubInv/rack-mount-enclosure-for-power/frontpanel/Parts/Mech/20X28CornerBracket.step

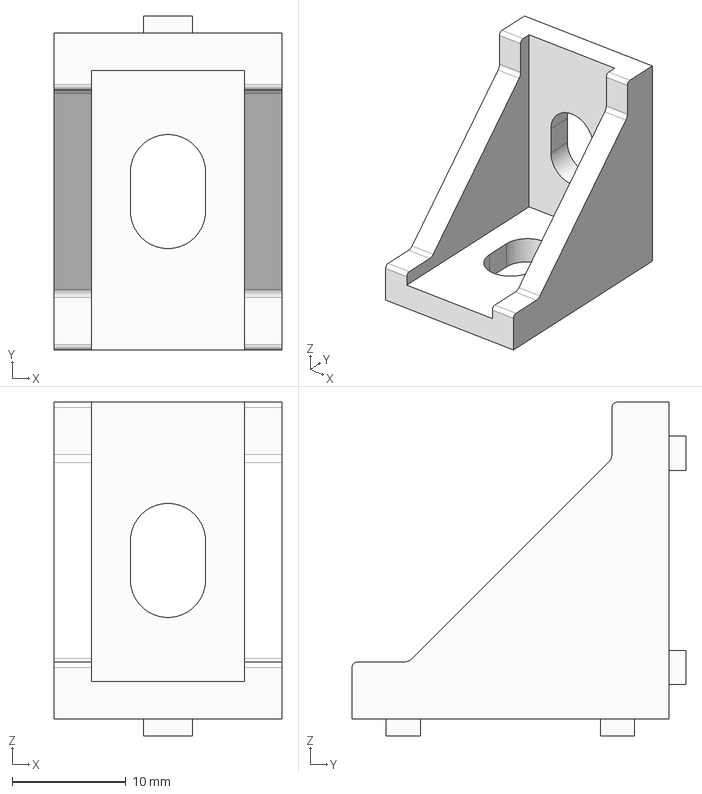
[picture p95: CAD file, 2023-08-03]
frontpanel/Parts/Mech/20X28CornerBracket.step
20.0 x 29.3 x 29.3 mm
