PubInv/rack-mount-enclosure-for-power/Plant20x30inch/AngleIron20inch.FCStd

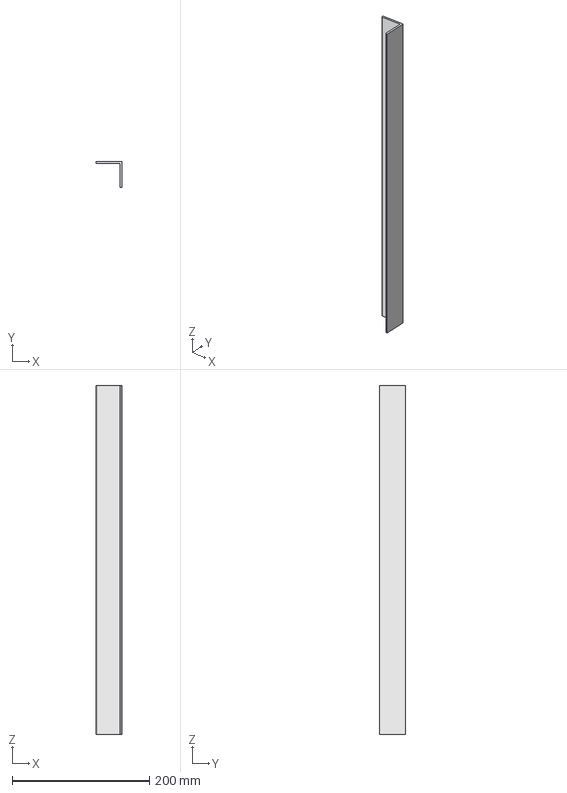
[picture p96: CAD file, 2024-07-16]
Plant20x30inch/AngleIron20inch.FCStd
38.1 x 38.1 x 508.0 mm
