PubInv/rack-mount-enclosure-for-power/frontpanel/frontpanel-PartFrontPanel2frontpanel2.step

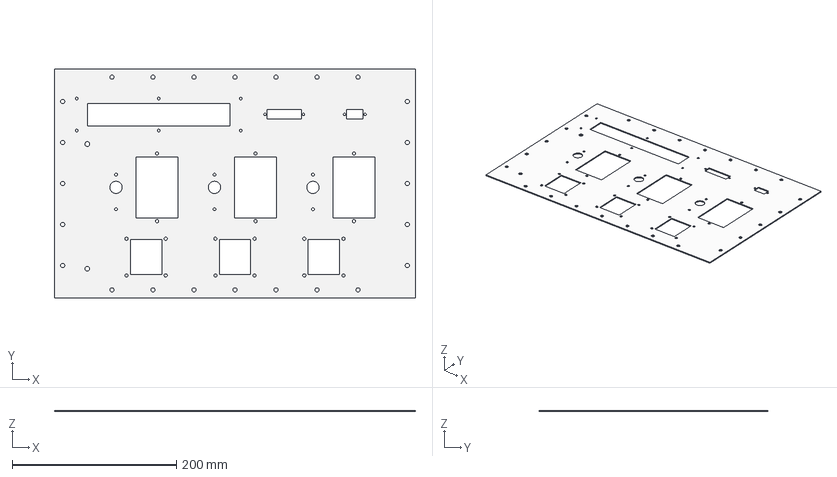
[picture p97: CAD file, 2023-07-31]
frontpanel/frontpanel-PartFrontPanel2frontpanel2.step
440.0 x 279.4 x 1.57 mm
