PubInv/rack-mount-enclosure-for-power/frontpanel/Parts/Mech/Decora cover v5.step

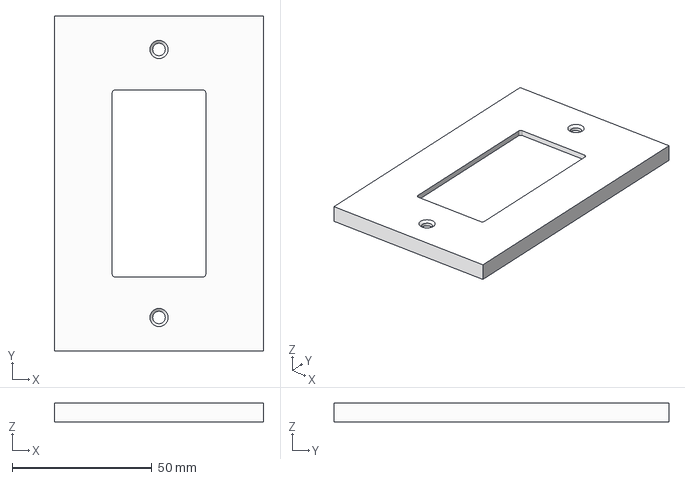
[picture p98: CAD file, 2023-08-03]
frontpanel/Parts/Mech/Decora cover v5.step
75.0 x 120.0 x 6.70 mm
