PubInv/rack-mount-enclosure-for-power/Plant20x30inch/AngleIron30inch.FCStd

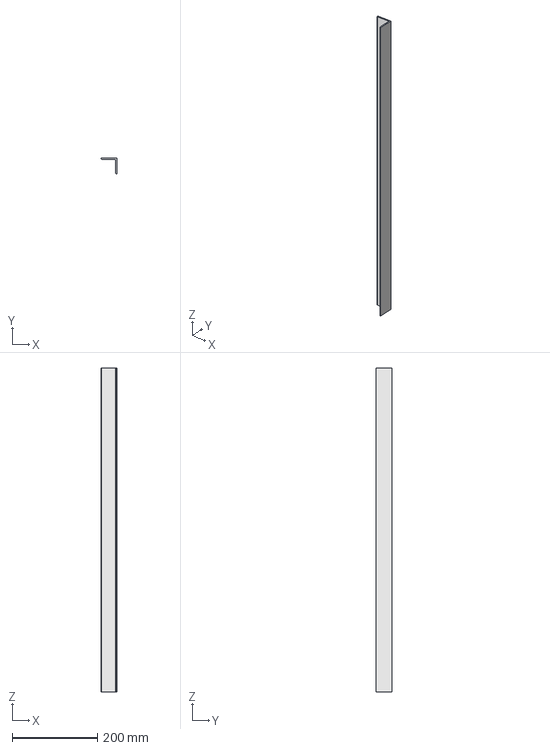
[picture p99: CAD file, 2024-07-16]
Plant20x30inch/AngleIron30inch.FCStd
38.1 x 38.1 x 762.0 mm
