PubInv/rack-mount-enclosure-for-power/enclosure/ThreeU/ThreeU_Chassis-BodyRearPanelWithHoles20240705_1543.step

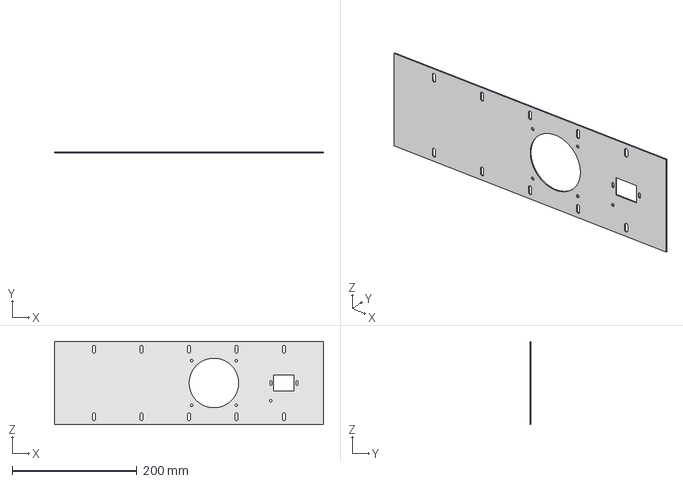
[picture p100: CAD file, 2024-07-05]
enclosure/ThreeU/ThreeU_Chassis-BodyRearPanelWithHoles20240705_1543.step
431.8 x 1.59 x 133.3 mm
