PubInv/rack-mount-enclosure-for-power/frontpanel/Parts/Mech/alu extrusion profile 2020.step

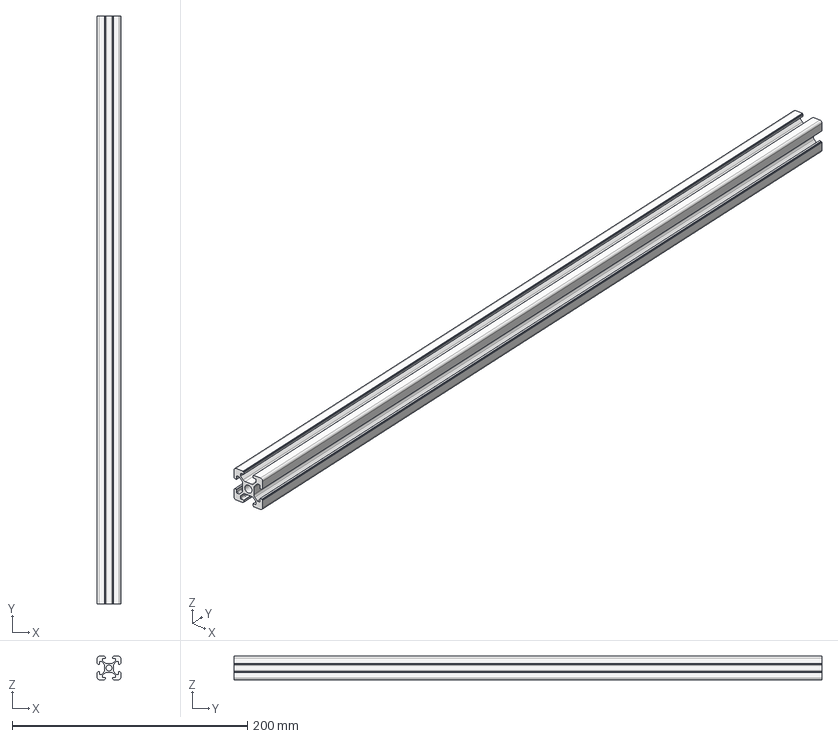
[picture p101: CAD file, 2023-08-03]
frontpanel/Parts/Mech/alu extrusion profile 2020.step
20.0 x 500.0 x 20.0 mm
