PubInv/rack-mount-enclosure-for-power/enclosure/ThreeU/ThreeU_Chassis-PartChassisBodyChassis_18x15_20240701_1059.step

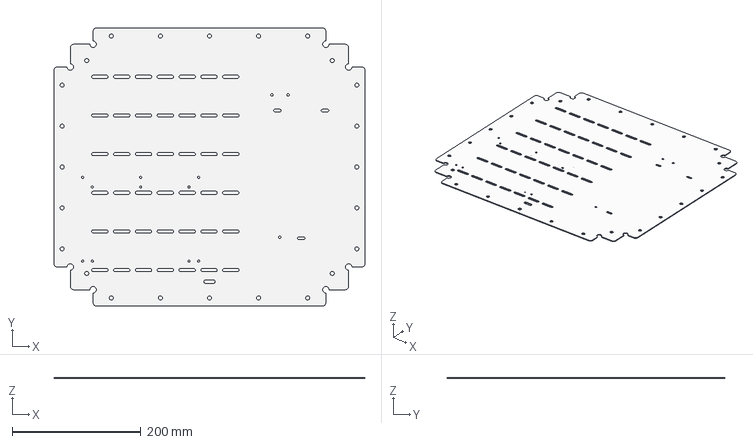
[picture p102: CAD file, 2024-07-05]
enclosure/ThreeU/ThreeU_Chassis-PartChassisBodyChassis_18x15_20240701_1059.step
482.6 x 431.8 x 1.59 mm
