PubInv/rack-mount-enclosure-for-power/frontpanel/frontpanel_Rev1_3.dxf

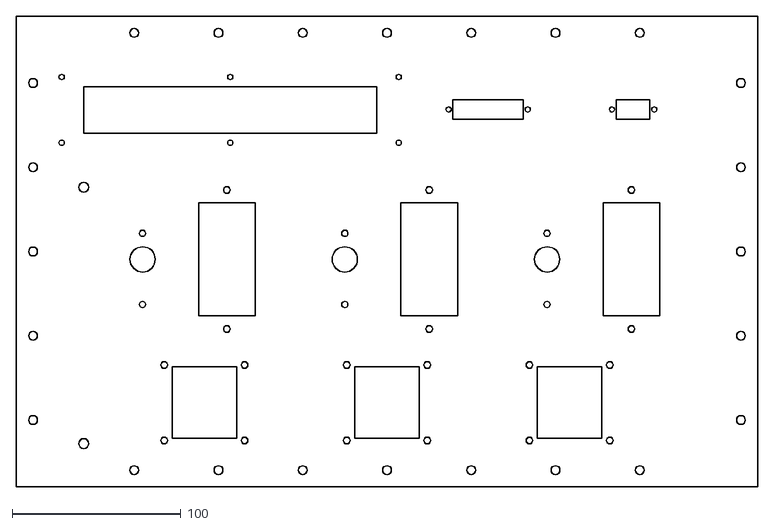
[picture p103: CAD file, 2023-04-05]
frontpanel/frontpanel_Rev1_3.dxf
440.0 x 279.4
