PubInv/rack-mount-enclosure-for-power/enclosure/RepRapDisplay/BigTreeTech/Dim_From_UserManual.png

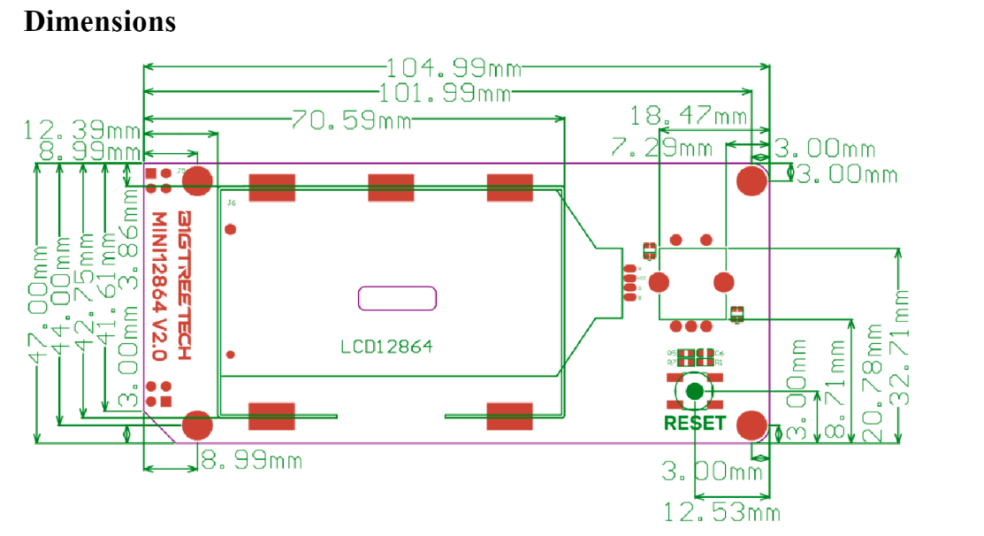
enclosure/RepRapDisplay/BigTreeTech/Dim_From_UserManual.png
