PubInv/rack-mount-enclosure-for-power/enclosure/Wiring Harness ThreeU/wiring_enclosure.png

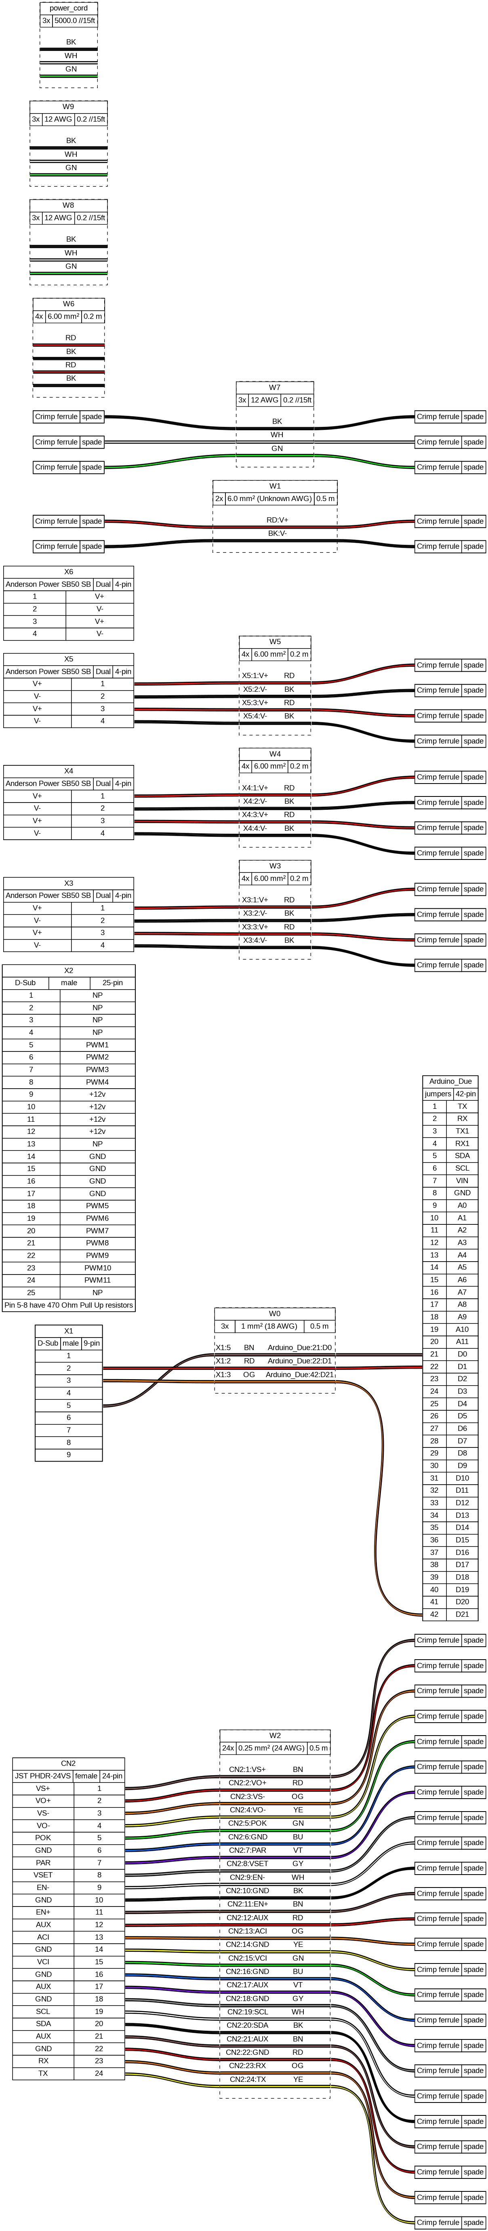
enclosure/Wiring Harness ThreeU/wiring_enclosure.png
