PubInv/rack-mount-enclosure-for-power/enclosure/ThreeU/PlantPanelWithO2Dimensions20250806.pdf

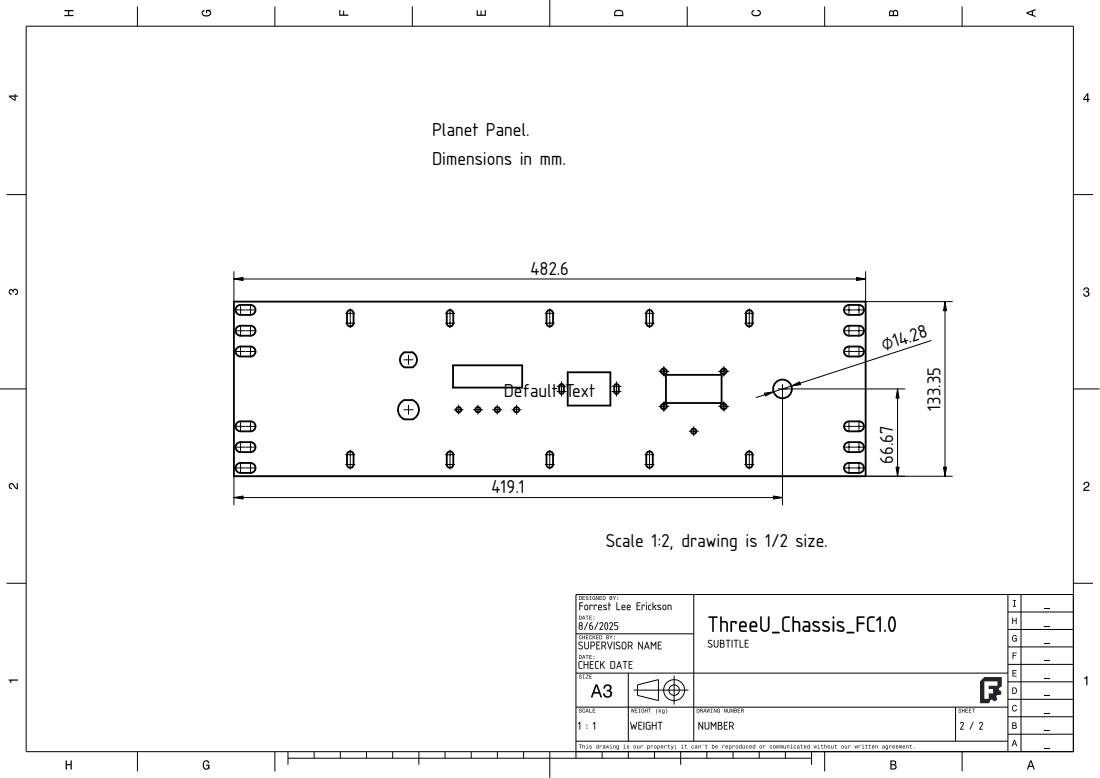
[picture p113: page 1]
Default Text; Planet Panel.

Dimensions in mm.

Scale 1:2, drawing is 1/2 size.
